xian-cong/Final-Year-Project-Nottingham/links and documents/project outline and planning report/Sample_Project Outline and Planning Report NJ-MEng-22-02-70_.pdf

## The University of Nottingham

## Faculty of Engineering

## Department of Electrical and Electronic Engineering

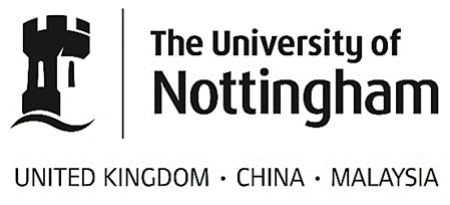
[picture p23: figure]

### EEEE4077 Project Outline and Planning Report

### Electrical Machine Condition Monitoring System

AUTHOR | : | Joel Wong Zi Xu
ID | : | 20208685
SUPERVISOR | : | Ir. Ts. Nandan Ganesh Jeyabalan
MODERATOR | : | Dr Mumtaj Begam
DATE | : | 21st Oct 2022

## Contents

1. Introduction | 1
2. Problem Statement | 1
3. Background Information | 2
3.1. Motor Faults | 2
3.2. Measurement of Vibration of Motors | 2
3.3. Measurement of Voltage of Motors | 3
3.4. Measurement of Current of Motors | 4
3.5. Measurement of Temperature of Motors | 4
3.6. Wave and Spectrum analysis | 5
3.7. IoT Technology | 6
4. Aim and Objectives | 6
4.1. Aim | 6
4.2. Objectives | 6
4.3. Deliverables | 6
5. Proposed Methodology | 7
6. Industrial Relevance | 7
7. Risk and Mitigations | 8
8. Project Timeline | 8
9. Appendix | i
References | i
Gantt Chart | iii
Project Specifications | iv

1

### 1. Introduction

As the operation of a motor continues in constant action, the likelihood of its failure increases as its operating conditions degrades and the machine becomes more and more vulnerable to wearing and aging. Based on the research, majority of motors become defective due to faults while only a mere 10% become inoperable due to old age [1]. Detecting faults before the occurrence of permanent damage is the intention of motor condition monitoring or alternatively, motor health monitoring, which is essential in preventing inner mechanical complications and prolonging the life of a motor [2].

Additionally with the advent of Internet of Things (IoT) technology, machines and devices are now able to be connected to exchange data with one another using the internet as its communication host [3]. Such technology has already been interfaced with the concept of motor condition monitoring in order to enhance the accessibility and control aspects of a motor health monitoring system. An example of such a system has proved its availability by allowing its user access to information of the motor, while away, by the usage of an Arduino compatible Wi-Fi module, the ESP8266, which in turn allows the motor monitoring system to pass the data from its motor monitoring sensors onto a webserver and therefore allowing access of its sensor information, via the internet, worldwide [4].

From literature review [1], [5], The condition of a motor is commonly measured through four parameters, these include: firstly, the motor temperature, which are usually used to gauge the condition of the bearing, ambient stator temperature. Secondly, the parameter of current which is used to determine the health of the windings as well as the mechanical system of the motor. Thirdly, the measurement of voltage which is used to judge the condition of the voltage supply as well as the power factor of the motor. Lastly, the intensity of the motor vibration which can be used to reveal issues in air-gap variation, misalignment, broken rotor bars and other mechanical motor faults.

This project focuses on the creation of a condition motoring system for a motor that is capable of detecting faults from the usage of information by sensors. Additionally, the system would also be interfaced with Wi-Fi technology in order to allow the information tracked to be available online and hence anywhere via the access of the internet.

### 2. Problem Statement

Failure of components awaits the operation of a motor the longer it remains in use as its parts are exposed to the wear and age from working [1]. The failure of parts of the motor vital to its functioning can begin to occur in the stator, rotor as well as upon the eccentricity of the motor where they are the result of the worn damaged parts which can include but are not limited to shorted coil windings, the breaking of rotor bars and the wearing of bearings respectively [6]. Consequently, the machine deteriorates as the faults add up, gradually becoming unreliable or even dangerous for operation. At the level of a large and complex industrial plant, the collection of failures is catastrophic and may result in the waste of millions of dollars for any rehabilitation and at the worst scenarios, a large-scale life-threatening accident [5]. The solution lies at the research of motor condition monitoring where the faults can be detected at the moment of their occurrence or even pre-occurrence and hence avoiding the disasters that may result from such motor failures.

2

### 3. Background Information

### 3.1. Motor Faults

As a motor remains in operation, wearing and aging can occur upon its body and this provides the root for the development of motor faults [1]. A machine fault can be described as any incident occurring within its machinery that obstructs the designed function of the machine [6]. Such faults can be defined into two categories: Internal faults, which includes component failures such as misalignment of motor sheets, coils, coupling, rotors & shaft, broken rotor bars or even damaged bearings whereas external faults are due to interactions with the loading, power supply as well as nearby environment and this includes overloading, environmental overheating, pollution and even unstable voltage [6]. The origin of faults are generally caused by stresses and careless operation, these can stem from several types, for instance, stator or armature faults are often traced to insulation problems which itself may be due to a collection of problems such as overheating of winding or stator core, loose bracing in the end winding, dirt contamination or even leaking from the cooling systems whereas damages of the rotor bar and end-rings mainly occur as a result of overheating, unbalanced magnetic forces, manufacturing issues as well as fatigued parts [7].

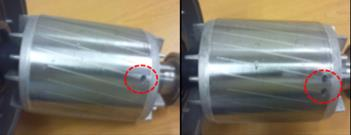
[picture p24: figure]

Figure 1: Rotor with one and two broken bars [8]

### 3.2. Measurement of Vibration of Motors

Vibrations generated by motors can be measured via the use of an accelerometer, through this, any vibrations produced as a result of any unintended impact of machinery can be detected; such vibration will appear at its characteristic frequency caused by the interference of the present defect [9]. As machinery failure usually manifests as vibration or as changes in vibration pattern due to their physical nature, vibration of motors is often used to monitor heavy physical defects that are often in rotation such as gears, shaft & rotors, rolling element bearings, journal bearings, flexible coupling as well as electrical machines [5]. The types of faults commonly to be detected via measurement of vibration are shown in Table 1:

3

Table 1: Faults that can be detected with vibration analysis [5]
Item | Fault
Gears | Tooth messing faults, Misalignment, Cracked and/or worm teeth, Eccentric gear
Rotors and shaft | Unbalance Bent shaft Misalignment Eccentric journals Loose components Rubs Critical speed Cracked shaft Blade loss Blade resonance
Rolling element bearings | Pitting of race and ball/roller Spalling Other rolling elements defect
Journal bearing | Oil whirl Oval or barrelled journal Journal/bearing rub
Flexible coupling | Misalignment Unbalance
Electrical machines | Unbalanced magnetic pulls Broken/damaged rotor bars Air gap geometry variations Structural and foundation faults Structural resonance Piping resonance Vortex shedding

### 3.3. Measurement of Voltage of Motors

The measurement of motor voltage is usually best suited to gauge the health of the supply voltage connected to the motor, via its phasing and balance, as well as the power factor of the motor [1]. Additionally, the measurement of the motor voltage has also been demonstrated to have the ability to replace the measurement of vibration in detecting physical faults as well as physical failure, for instance, a damaged rotor which exhibit high frequency disturbances to the

4

rotor mechanical speed will begin to affect the resultant magnetic field of the air gap as the rotor bar current fail to overcome the disturbance rapidly and hence causing induced voltages in the stator windings to be disturbed, therefore allowing possible detection of damaged rotor via voltage measurement [10].

### 3.4. Measurement of Current of Motors

To assess the condition of the motor windings as well as to gauge the load undertaken by the motor, the measurement of motor current can be performed [1]. Additionally, the current measured could be transformed into a decibel-frequency range via Fast Fourier Transform to provide information regarding frequencies due to fault which are affecting the general waveform of the current; fault can be detected as the current waveform measured would be different with and without the presence of faults [11], [12].

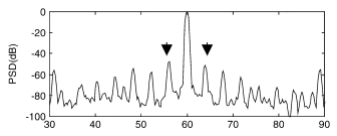
[picture p25: figure]

Figure 3: A Plotted Graph of MCSA of a Healthy Motor [8]

### 3.5. Measurement of Temperature of Motors

The motor temperatures can be determined via the usage of thermocouples, optical pyrometers, thermography, and resistance thermometer [5]. Temperatures measured in a motor are, in normal circumstances, generated from the magnetic losses within the rotor & stator, the resistive losses (I²R), friction as well as the motor windage [1]. Via temperature analysis, faults related to wearing due to insufficient lubricant can be monitored and prevented where additionally, the detection of overheating, which can subject organic material within the insulation of the stator winding to deteriorate, can also be identified, and mitigated [5].

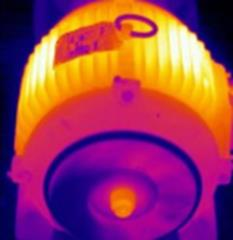
[picture p26: figure]

Figure 4: Thermal RGB image of a motor showing levels of temperature throughout motor [13]

5

### 3.6. Wave and Spectrum analysis

The most common two ways to analyse and detect faults and failures within a motor is, firstly, by performing a time-domain analysis which is via inspecting the measured data (ie. Voltage, Temperature, Current, Vibration, etc.) from the sensors as a plot against the time as this allows a clear investigation of the direct and raw data from the sensor output; the second method is by converting the time-domain measured data into the frequency domain, typically done using fast Fourier transform (FFT), where faults can be observed due to their specific unique frequencies generated to due to their existence appearing as peaks alongside the expected frequencies of a normal working motor should the motor in evaluation possesses one or more faults [5]. An example of this has been mentioned with the description of MCSA where the current measured could be represented as a decibel-frequency via Fast Fourier Transform [10]. Similarly, another example can be found in the frequency spectrum of the vibrations measured, done using Fourier Transform, where the frequency of each component is known and hence where the peaks appear at the frequency of that particular component, a fault can be confirmed to exist at that particular component [9]. Furthermore, as the existence of noise may be recorded as well such that the frequency spectrum represented might be disturbed and become inaccurate, averaging of the values before the conversion into the frequency spectrum could be done to reduce the presence of noise [11]. From this, it can also be concluded that the use of multiple types of spectrum analysis (ie. Voltage, current, vibration, etc.) can be done for each fault in order to clearly assess the existence of faults and avoid errors.

Figure 5: Voltage Frequency Spectrum of a motor with Broken Rotor Bars at 80% of the motor full load [8]

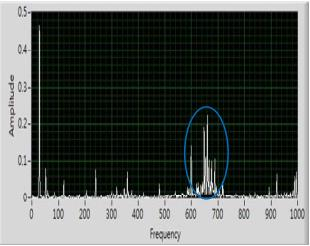
[picture p27: figure]

Figure 6: Vibration Frequency Spectrum of a motor indicating fault at the rotor [14]

6

### 3.7. IoT Technology

Internet of Things (IoT) can be defined as the connection of devices and objects to share data and to communicate using the internet as a pathway [3]. Through the usage of this technology, complications due to physical components necessary for data transfer between sensors in condition motoring are eliminated, additionally, the absence of wires allows better strategical placement of the sensors onto positions previously inconceivable due the space needed for the physical trail of wires connected [15]. An example of such a system which integrates IoT and Motor Condition Monitoring has been demonstrated to be possible where the system was capable of measurement of Voltage, current as well as vibration along with the fact that it can detect the existence of faults and alert the user anytime at its occurrence, wirelessly to anywhere through an internet connection [4].

### 4. Aim and Objectives

### 4.1. Aim

The main focus of this project is to design and program a condition monitoring system for electrical machines with the ability to transfer its recorded information over a wireless transfer data system with a user interface

### 4.2. Objectives

- Design and develop a condition monitoring system for the electrical machines.
- Analyse the performance by monitoring the condition of electrical machines using the developed system.
- Classify the abnormalities found in monitoring the electrical machines by suing the developed system.
- Develop a wireless transfer data system to integrate with the developed system for user interface.

### 4.3. Deliverables

- Identify the parameters of the electrical machines that will be used for condition monitoring.
- Design the condition monitoring system by integrating with the electrical and mechanical sensors.
- Test the developed system to ensure the condition of the machines is monitored based on the relevant parameters.
- Develop a wireless transfer data system to transfer the monitored parameters for user interface.

7

### 5. Proposed Methodology

- Literature review and Research: At the initial stages of the project, the essentials of motor condition monitoring would need to be understood. The various types of faults occurring within a typical motor as well as the methods utilized for faults detection would need to be familiarized for the identification of failures. Additionally, concepts related to IoT technology and software would need to be read upon for the basis of a wireless transfer data system. Lastly, a study upon tutorials would need to be carried out in order for the proper usage of the different sensors and modules
- Integration of Sensors to the Motor: The identification of errors stems pivotally from the positioning of the sensors to the right connection relative to the motor in evaluation in order for accurate detection of faults
- Programming Wireless Transfer of Data from Sensors: Coding of a program as well as strategic integration of a Wi-Fi module to acquire and manage information gathered by the sensor to display over to the user of the system, wirelessly
- Simulating Faults: Motors have to be physically manipulated in order to mimic the condition of a faulty motor so as to assess the validity of the constructed condition monitoring system via comparison of detected data and faulty pattern of information from reviewed literature
- Classifying Faults: Information from different sensors have to be integrated cohesively both physically and through the developed program in order to determine the pattern of data that will occur when measured by different sensors for each specific fault

### 6. Industrial Relevance

On the scale of large industrial manufacturing plants, failure of machines such as a motor within its complex process would risk expensive operating costs due to maintenance of incapacitated components, the loss of possible production that could have been without the occurrence of failed machines as well as putting the lives of operation crew members in serious endangerment [5].

To prevent such complications, logically, the failure or faults of the machine must be detected at its occurrence or even prior to it. In condition monitoring of motors, failures such as stator winding and rotor faults can be reliably detected as each type of fault appear with distinct characteristics such as when measured with a vibration sensor (accelerometer), current sensor or even a voltage sensor which means that faults have the possibility of being instantly identified and hence preventing resulting consequences [8], [9]. To further ensure proper monitoring of a large complex plant, several types of strategic maintenance of the components could be carried out of which motor condition monitoring could be advantageous to. Firstly, there exists a predictive type of maintenance known as Condition-based maintenance which is maintenance done where restoration of a part is initiated due to noticeable wearing detected as result of a change in its monitored parameter [5]. Other types of maintenance include proactive maintenance which is based on analysis of failure as well as preventative maintenance which include checkups once every duration in a set time; the implementation of such strategies has been analyzed to eliminate factory downtime as well as in assisting the avoiding of mistakes which directly leads to enhancing the efficiency of a plant to its fullest potential [16].

8

Additionally, the rise of IoT and its integration means condition monitoring does not have to be physical presence based as the information from sensors can be passed via the internet and hence allowing workers to monitor motors even while away from the workplace [4].

### 7. Risk and Mitigations

In this project, several types of sensors and modules are implemented to create a sensor system, each with its own unique set of programming code for the manipulation of its sensor, as such, the combination of all sensors and its individual programming to exchange data may prove to be time-consuming and difficult. To ease the process, certain sensors should be programmed and worked on first before integrating other sensors to prevent a chaotic combination of programming. Furthermore, there could exist a limit to the type of fault that can be allowed to be simulated for testing purposes due to the dangerous nature of certain failure such as, but are not limited to, high current short circuit of the stator winding as well as high speed rotation of broken rotor bars. To avoid serious injury, the use of personal protective equipment (PPE) such as safety googles could be utilized as well as performing the simulated of faults during the presence of the supervisor to prevent accidents due to inexperience.

### 8. Project Timeline

In the Autumn semester, the focus of tasks will be on Literature review upon the various types of faults, the ways to detect them as well as forming the basis of wireless transfer of data from sensors. Later, the integration of sensors to the motor would be carried out before the simulation of faults can be done to confirm the validity of the measurement of the sensors as well as to record motor fault behaviour. In the Spring Semester, the development of a wireless data transfer program with the ability to classify motor faults can be worked upon based on the work from the previous semester before the final task of motor fault classification from the data of various sensors will be carried out. More details of the time plan can be found in the Gantt Chart in the appendix.

i

### 9. Appendix

References

[1] R. Loiselle, Z. Xu, and I. Voloh, “Essential motor health monitoring,” Record of Conference Papers - Annual Petroleum and Chemical Industry Conference, vol. 2016-March, no. December, pp. 8–13, 2016, doi: 10.1109/PCICON.2015.7435126.
[2] D. Mirabbasi, G. Seifossadat, and M. Heidari, “Effect of unbalanced voltage on operation of induction motors and its detection,” ELECO 2009 - 6th International Conference on Electrical and Electronics Engineering, pp. 189–192, 2009.
[3] T. Muhonen, H. Ailisto, and P. Kess, “Standardization in Industrial internet (IoT) and Condition-Based Maintenance,” Proceedings at the Automaatio XXI …, no. March, 2015, [Online]. Available:
https://www.researchgate.net/profile/Heikki_Ailisto/publication/277668082_Standardization_in_Industrial_internet_IoT_and_Condition-Based_Maintenance/links/5570007508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
[4] N. Khan, F. Rafiq, F. Abedin, and F. U. Khan, “IoT Based Health Monitoring System for Electrical Motors,” pp. 6–11, 2019.
[5] P. Jayaswal, A. K. Wadhwani, and K. B. Mulchandani, “Machine fault signature analysis,” International Journal of Rotating Machinery, vol. 2008, 2008, doi: 10.1155/2008/583982.
[6] A. J. Bazurto, E. C. Quispe, and R. C. Mendoza, “Causes and failures classification of industrial electric motor,” Proceedings of the 2016 IEEE ANDESCON, ANDESCON 2016, pp. 4–7, 2017, doi: 10.1109/ANDESCON.2016.7836190.
[7] A. Choudhary, D. Goyal, S. L. Shimi, and A. Akula, “Condition Monitoring and Fault Diagnosis of Induction Motors: A Review,” Archives of Computational Methods in Engineering, vol. 26, no. 4, pp. 1221–1238, 2019, doi: 10.1007/s11831-018-9286-z.
[8] A. Shaeboub, M. Lane, U. Haba, F. Gu, and A. D. Ball, “Detection and diagnosis of compound faults in induction motors using electric signals from variable speed drives,” 2016 22nd International Conference on Automation and Computing, ICAC 2016: Tackling the New Challenges in Automation and Computing, no. September, pp. 306–312, 2016, doi: 10.1109/IConAC.2016.7604937.
[9] R. K. Patel, S. Agrawal, and N. C. Joshi, “Induction motor bearing fault identification using vibration measurement,” 2012 Students Conference on Engineering and Systems, SCES 2012, no. June 2015, 2012, doi: 10.1109/SCES.2012.6199058.
[10] F. Dalvand, A. Kalantar, S. Shokoohi, and H. Bevrani, “Time-domain bearing condition monitoring in induction motors using instantaneous frequency of motor voltage,” pp. 1–7, 2015, doi: 10.1109/sgc.2014.7150708.
[11] E. Geetha and C. Nagarajan, “Induction Motor Fault Detection and Classification Using Current Signature Analysis Technique,” Proc. IEEE Conference on Emerging Devices and Smart Systems, ICEDSS 2018, no. March, pp. 48–52, 2018, doi: 10.1109/ICEDSS.2018.8544272.
[12] M. Irfan, N. Saad, R. Ibrahim, and V. S. Asirvadam, “An intelligent diagnostic system for the condition monitoring of AC motors,” Proceedings of the 2013 IEEE 8th Conference on Industrial Electronics and Applications, ICIEA 2013, pp. 1248–1253, 2013, doi: 10.1109/ICIEA.2013.6566558.

ii

[13] S. Badoni and R. K. Jarial, “Health Monitoring of three phase induction motor using infrared thermography,” Proceedings of the 6th International Conference on Communication and Electronics Systems, ICCES 2021, pp. 156–160, 2021, doi: 10.1109/ICCES51350.2021.9489095.
[14] J. L. Jiang, H. C. Chang, and C. C. Kuo, “Operating monitoring and fault types classification for motors through vibration signal,” Proceedings - 2016 IEEE International Symposium on Computer, Consumer and Control, IS3C 2016, pp. 61–64, 2016, doi: 10.1109/IS3C.2016.26.
[15] X. Xue, V. Sundararajan, and W. P. Brithinee, “THE APPLICATION OF WIRELESS SENSOR NETWORKS FOR CONDITION MONITORING,” pp. 12–15.
[16] M. M. O. Kane and M. J. Sander, “Intelligent Motors Moving To The Forefront Of Predictive Maintenance”.

iii

Gantt Chart

Year 4 Individual Project Gantt Chart

Supervisor: Ir. Ts. NANDAN GANESH JEYABALAN | Legends: | Week of Moderator Meeting:
Project Code: NJ-MEng-21-02 | | Milestone:
Autumn Semester | Study Week | Exam | CNY Break | H Raya Spring Semester Break
| | October | | | January | February | March
| | | | | | November | | WEEK 13 | December WEEK 9 | WEEK 26 | WEEK 30 Tasks | April WEEK 22

Planning For Project Location and item Requirements HIRARC form and Securing Lab Workspace
Hardware Inspection and Sensor Component Research Finalising Project Objectives and Project Specification Hardware Research and Purchase Cost Estimation Writing Project Outline and Planning Report

Submition of Project Outline and Planning Report

SeptWEEK 4 | WEEK 5 | WEEK 6 | WEEK 7 | WEEK 8 | WEEK 10 | WEEK 11 | WEEK 12 | WEEK 14 | WEEK 15 | WEEK 16 | WEEK 17 | WEEK 18 | WEEK 19 | WEEK 20 | WEEK 21 | WEEK 23 | WEEK 24 | WEEK 25 | WEEK 27 | WEEK 28 | WEEK 29 | WEEK 31 | WEEK 32 | WEEK 33 | WEEK 34 | WEEK 35

Researching and Studying Electrical Machine Condition Monitoring Methods

Researching of Common Electrical Motor Faults
Literature Review of Electrical Machine Condition Monitoring via Sound and Vibration Literature Review of Electrical Machine Condition Monitoring via Voltage and Current Literature Review of Electrical Machine Condition Monitoring via Temperature Literature Review of Electrical Machine Condition Monitoring using IoT technology

Designing and Setting up Induction Motor Condition Monitoring System

Researching and Learning the Function of the Sensors and WIFi Module Coding of Program to Manage the Monitoring of Sensors and WiFi Module Physically Intergrating Sensors onto the Motor
Running Induction Motor to Ensure Accurate Measurement by Sensors Simulating Induction Motor Faults to Record Specific Motor Fault Behaviour

Development of Wireless Transfer Data System Interface

Coding of Program to Display User Interface for the Condition Monitoring System Coding of Program to Connect Software User Interface to Sensors used in Monitoring Coding of Program to Display the Correct Fault Information in Relation to the Detection

Classification of Motor Faults in the Motor Condition Monitoring System
Linking Pattern of Information detected from Different Sensors into the Common Fault Detected
Coding of Program to Display the Correct Fault Information from multiple Sensors in Relation to the Detection

Thesis, Documents and Presentation Writing Sections of Draft Thesis

Draft Thesis submission Writing Sections of Final Thesis

Final Thesis & Logbook Submission Preparation of Roadshow
Presentation and Viva Preparation

Student Name: Joel Wong Zi Xu Student ID: 20208685

iv

Project Specifications
Project Code | NJ-MEng-22-02
Supervisor | Ir. Ts. Nandan Ganesh Jeyabalan
Moderator | Dr Mumtaj Begam

Project
Description

Project Title: Electrical Machine Condition Monitoring System

The term reliability is a criterion that must be considered when selecting an electrical machine and its drive system for a particular load. As the cost of machines and drives varies proportionally to their reliability status, studies have been conducted throughout the world to achieve one ultimate goal – to produce a machine and drive system with higher reliability and minimum cost spent in manufacturing it. Therefore, condition monitoring is an important part in ensuring the performance and life span of the electrical machines maintained and improved. This project aims to design an Electrical Machine Condition Monitoring System in order to better monitor the performance and improve the overall efficiency of the electrical machines.

Project Objectives | 1. Design and develop a condition monitoring system for the electrical machines. 2. Analyse the performance by monitoring the condition of electrical machines using the developed system. 3. Classify the abnormalities found in monitoring the electrical machines by suing the developed system. 4. Develop a wireless transfer data system to integrate with the developed system for user interface.
Project Deliverables | 1. Identify the parameters of the electrical machines that will be used for condition monitoring. 2. Design the condition monitoring system by integrating with the electrical and mechanical sensors. 3. Test the developed system to ensure the condition of the machines is monitored based on the relevant relevant parameters. 4. Develop a wireless transfer data system to transfer the monitored parameters for user interface.
Target Discipline (You may check both) | ☑ Electrical and Electronic ☐ Mechatronic

v

HW/SW/Research Ratio | HW | SW | Research/Investigation/Design/Math
| 50 | 30 | 20
Lab Space Requirements | ☒ Fixed Space ☐ Ad-hoc Space ☐ Others. Please state.
Software (This is software usually supportedin the Software Lab) | Python, Arduino Programming Codes
Prepared By: | Reviewed By:
Ir. Ts. Nandan Ganesh Jeyabalan | Dr Mumtaj Begam
30th of September 2022 | 12 Oct. 2022
(Supervisor) | (Moderator)

# Electrical Machine Condition Monitoring System

# by Joel Zi Xu Wong

### Submission date: 24-Oct-2022 04:47PM (UTC+0100)

## Submission ID: 187347788 File name:

243058_Joel_Zi_Xu_Wong_Electrical_Machine_Condition_Monitoring_System_6299887_1057029960.pdf (525.9K)

## Word count: 4284 Character count: 25819

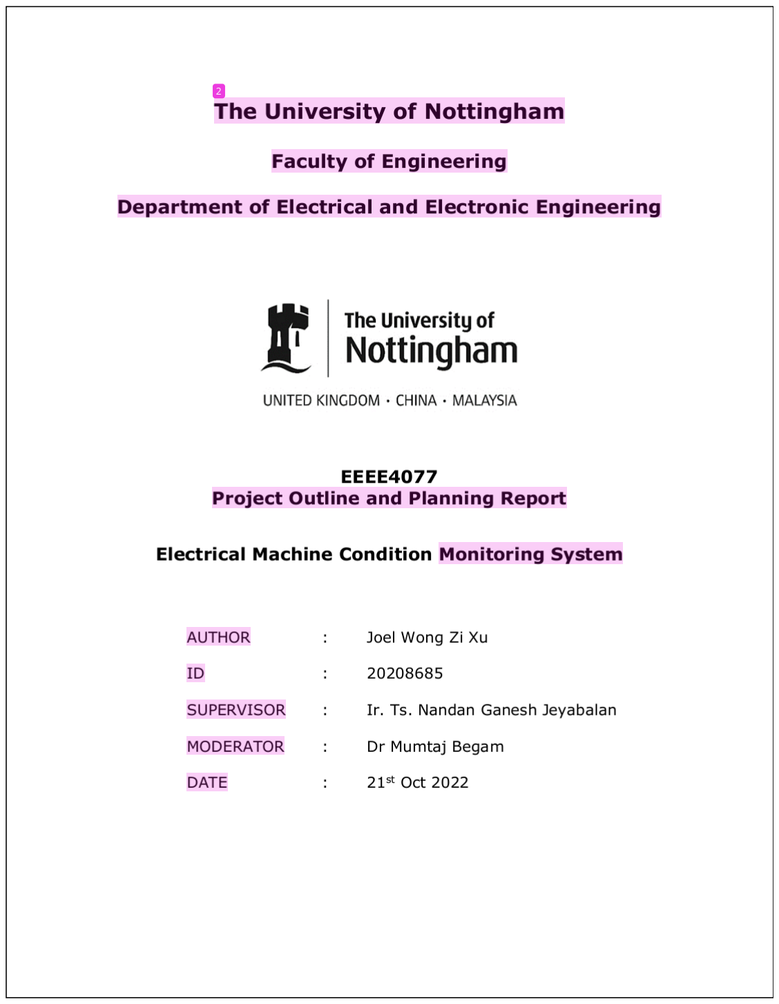
[picture p28: page 17]

2

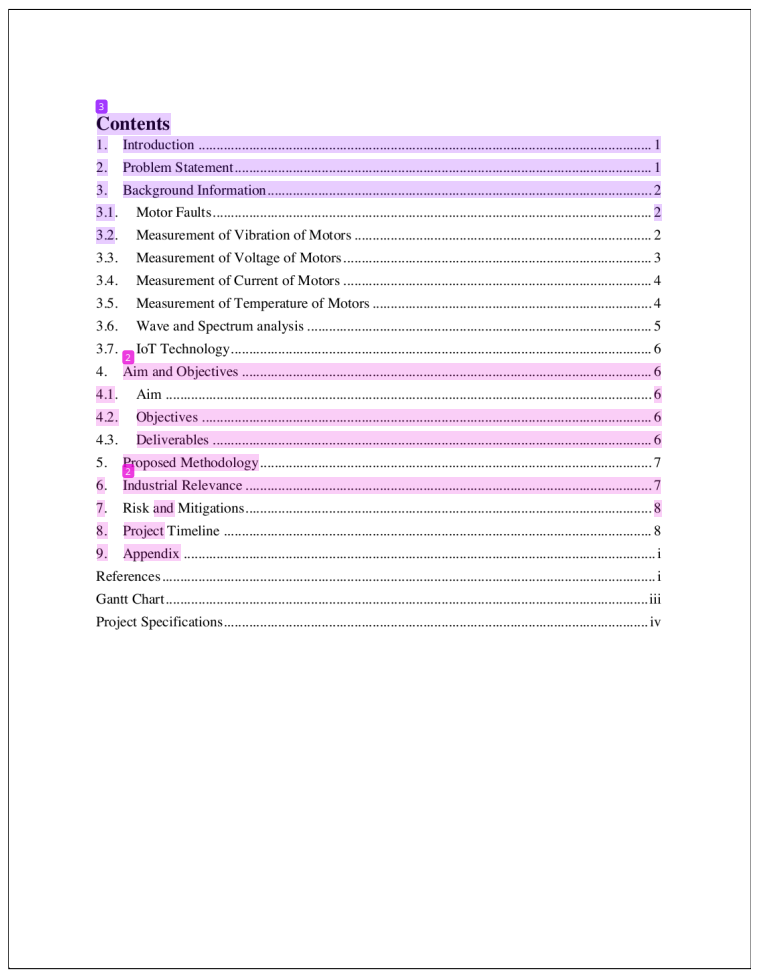
[picture p29: page 18]

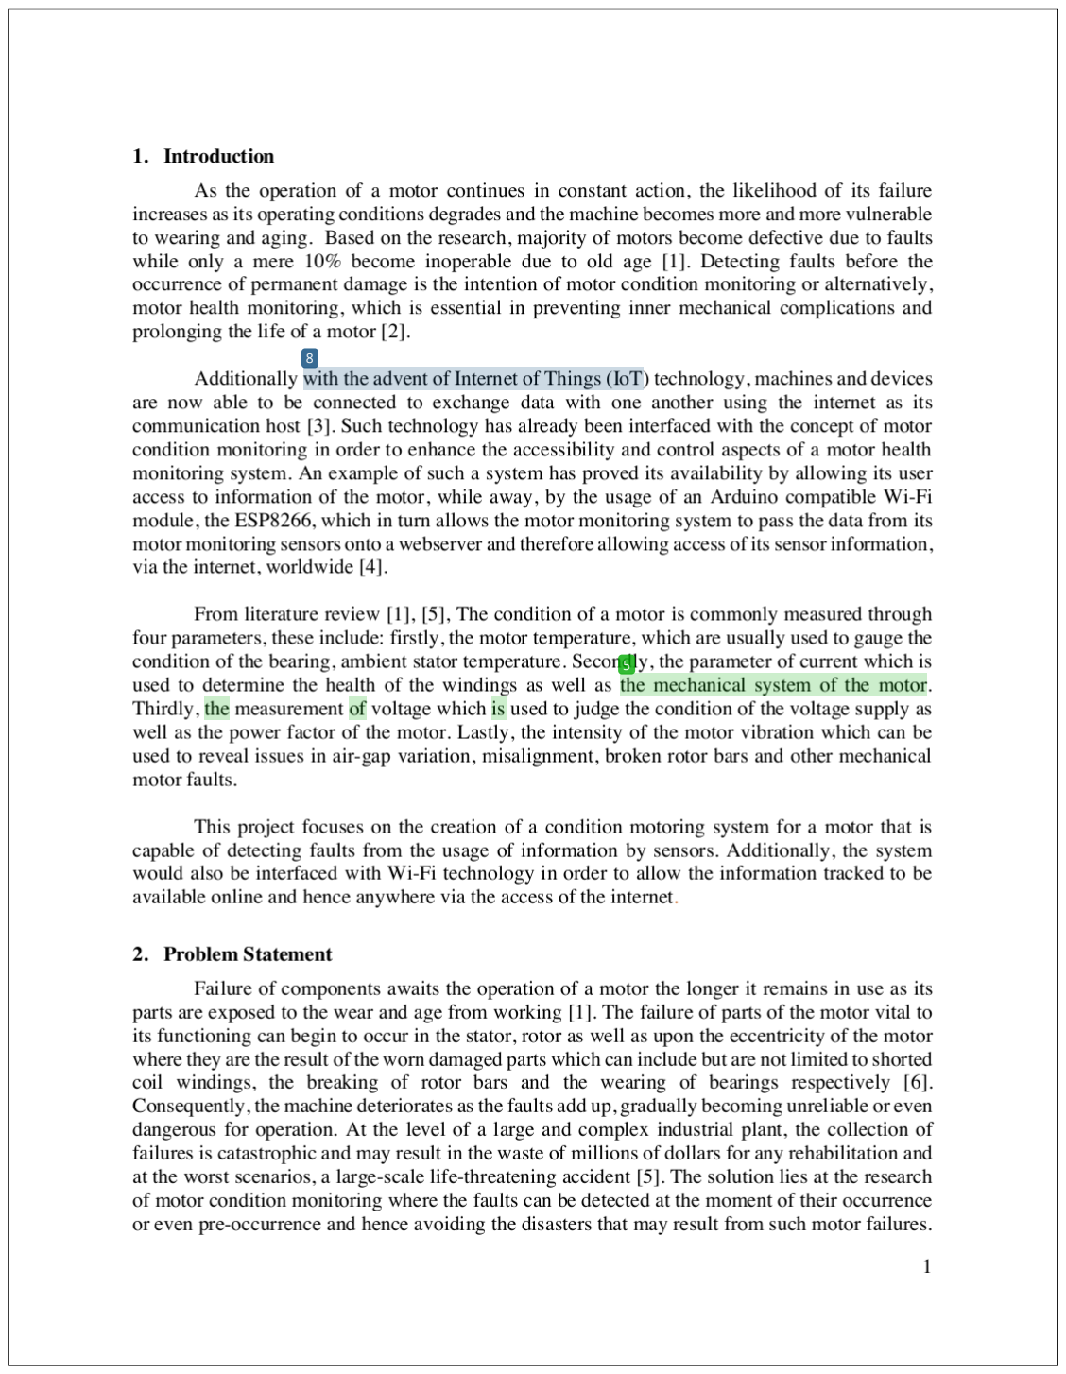
[picture p30: page 19]

5

8

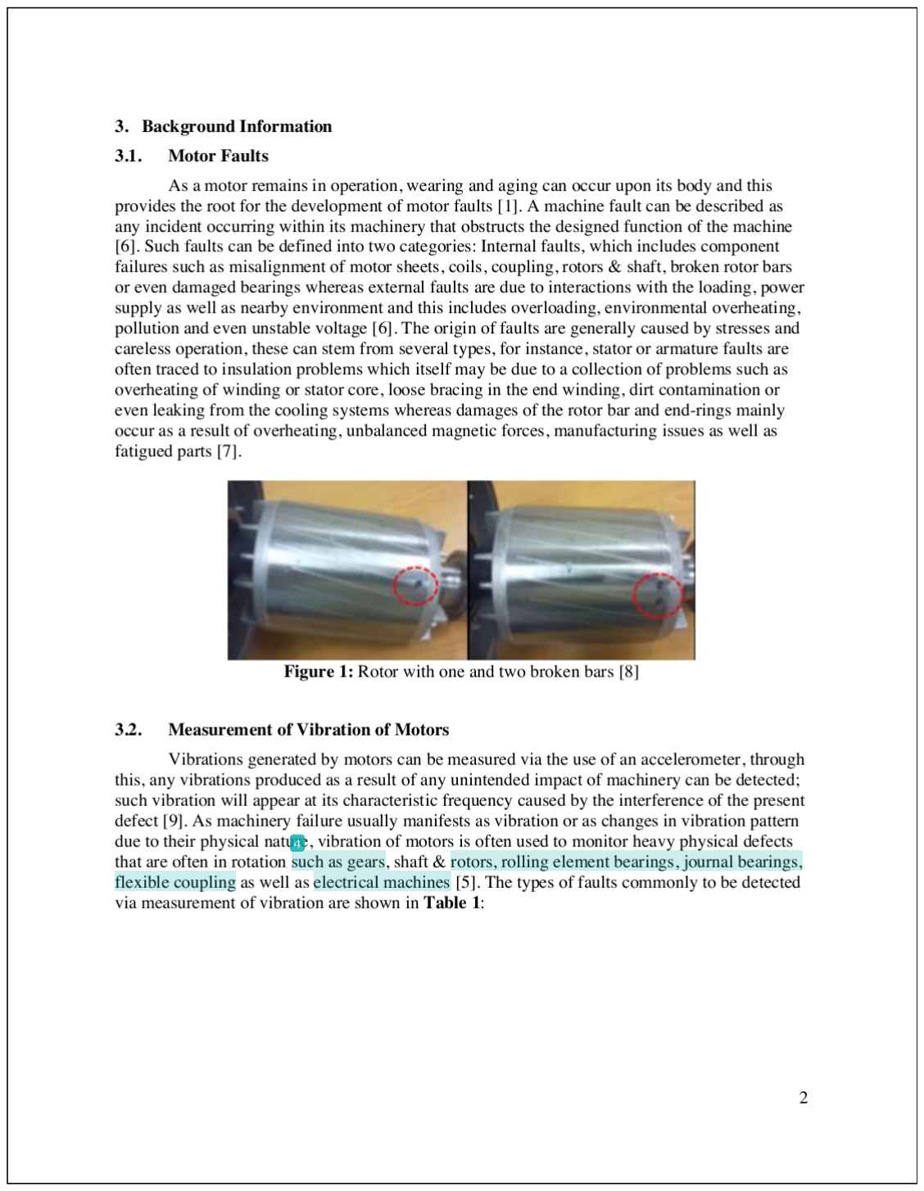
[picture p31: page 20]

4

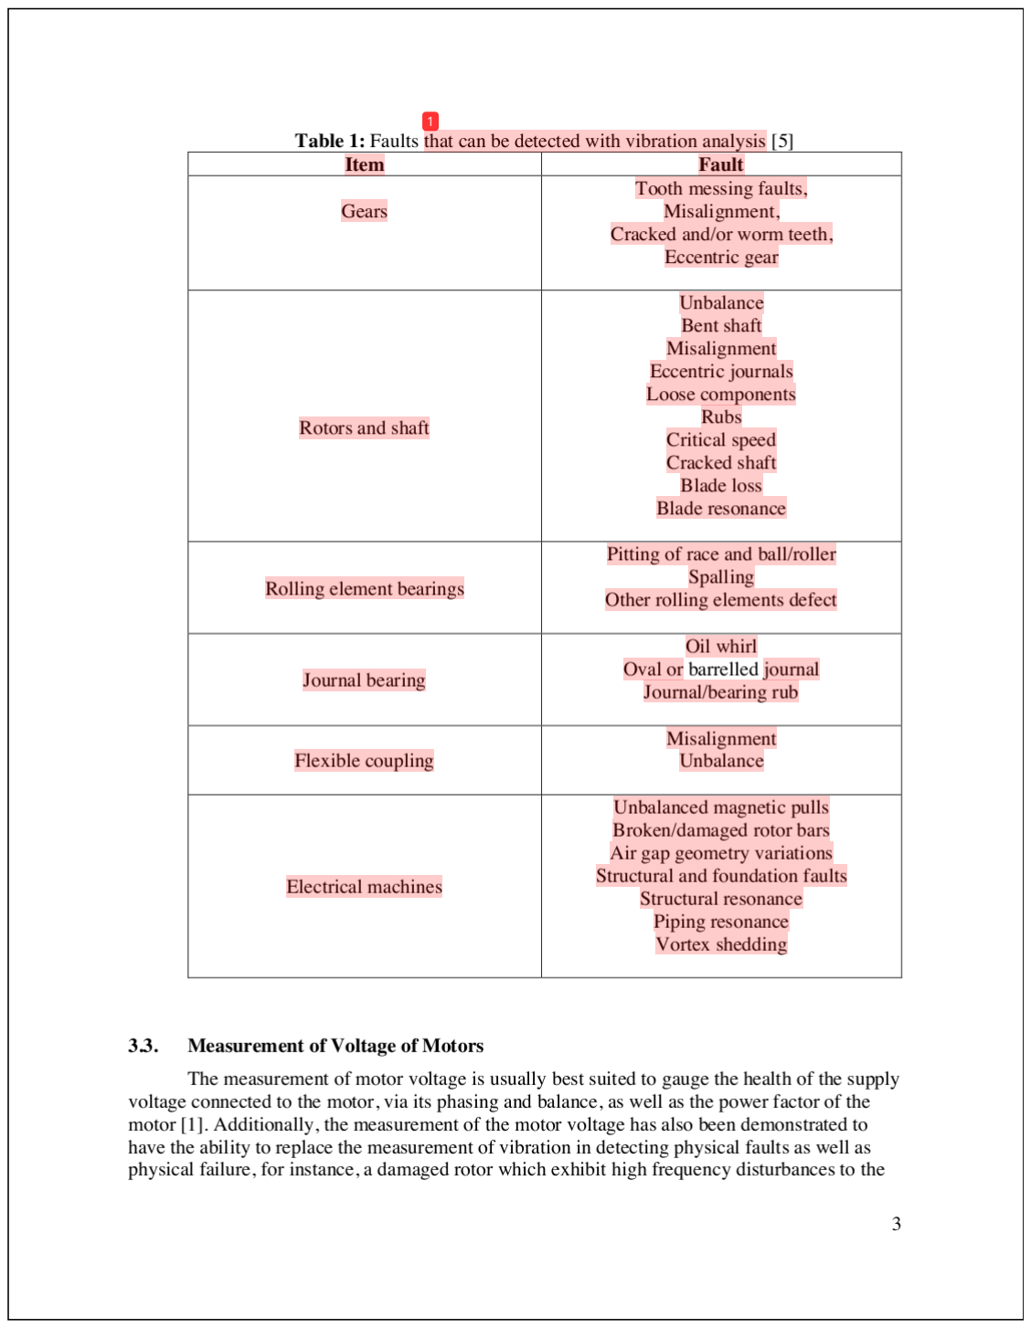
[picture p32: page 21]

1

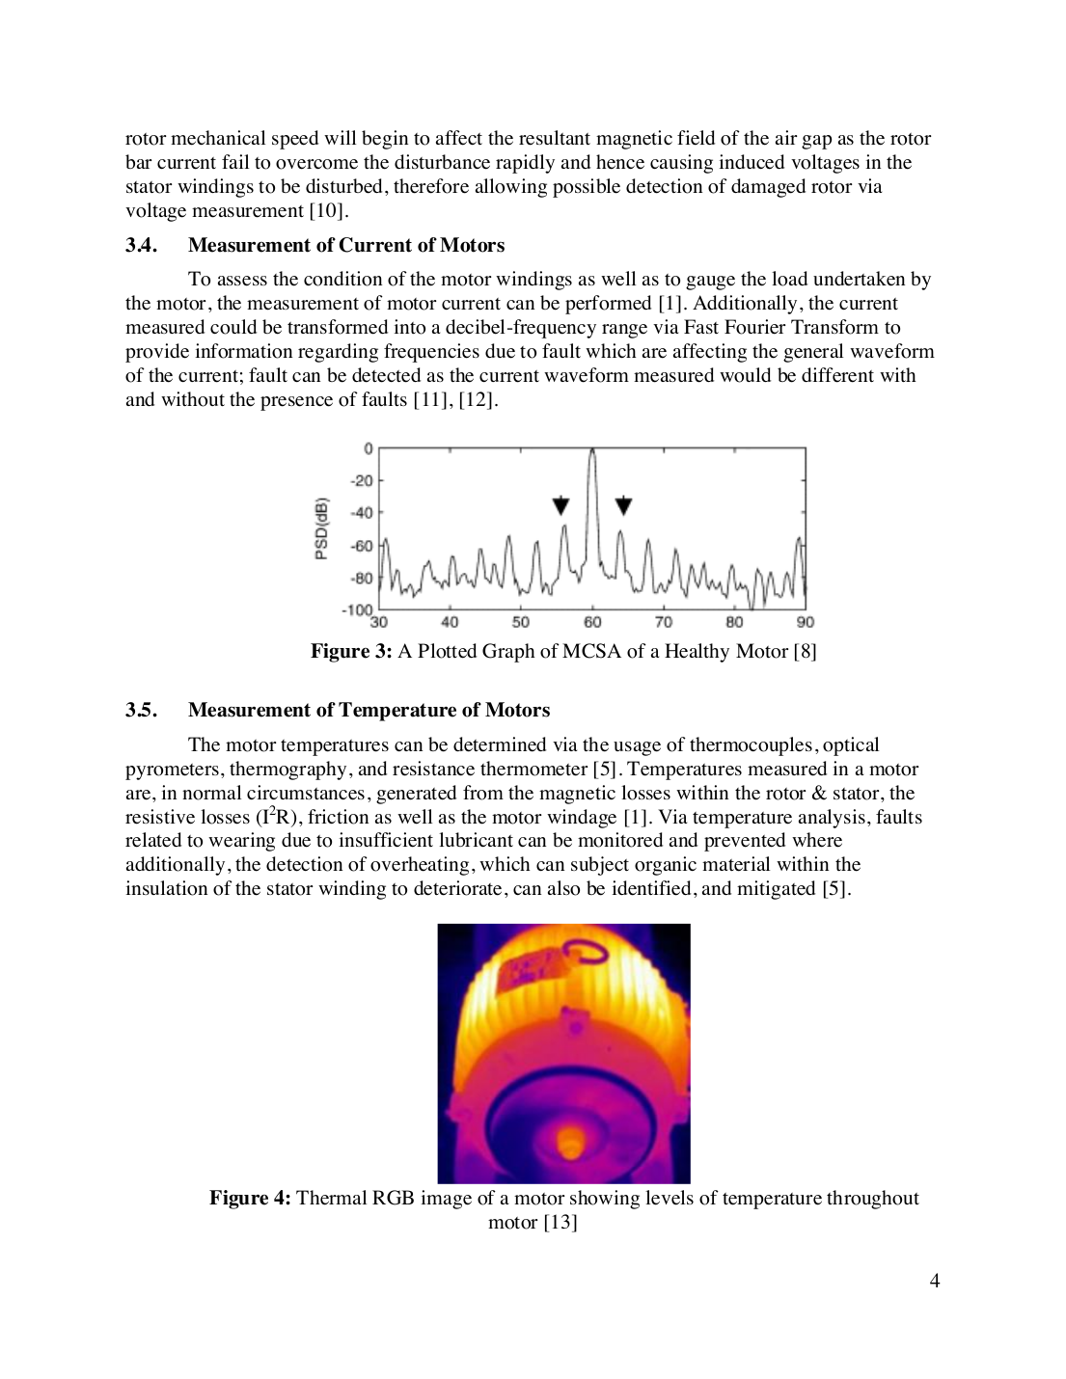
[picture p33: page 22]
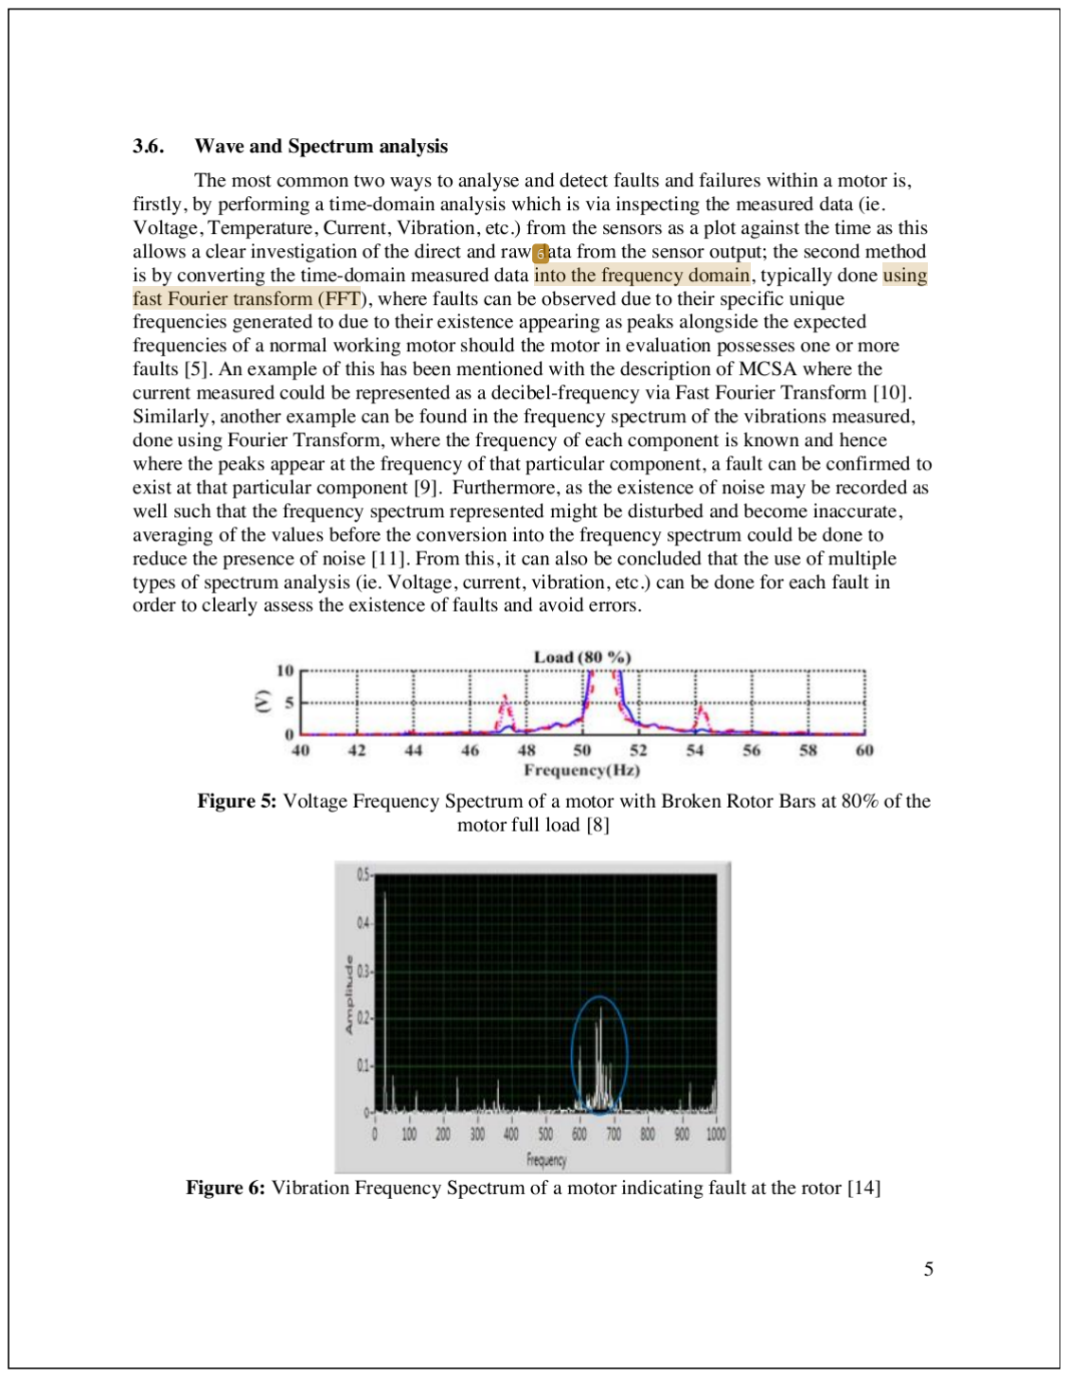
[picture p34: page 23]

6

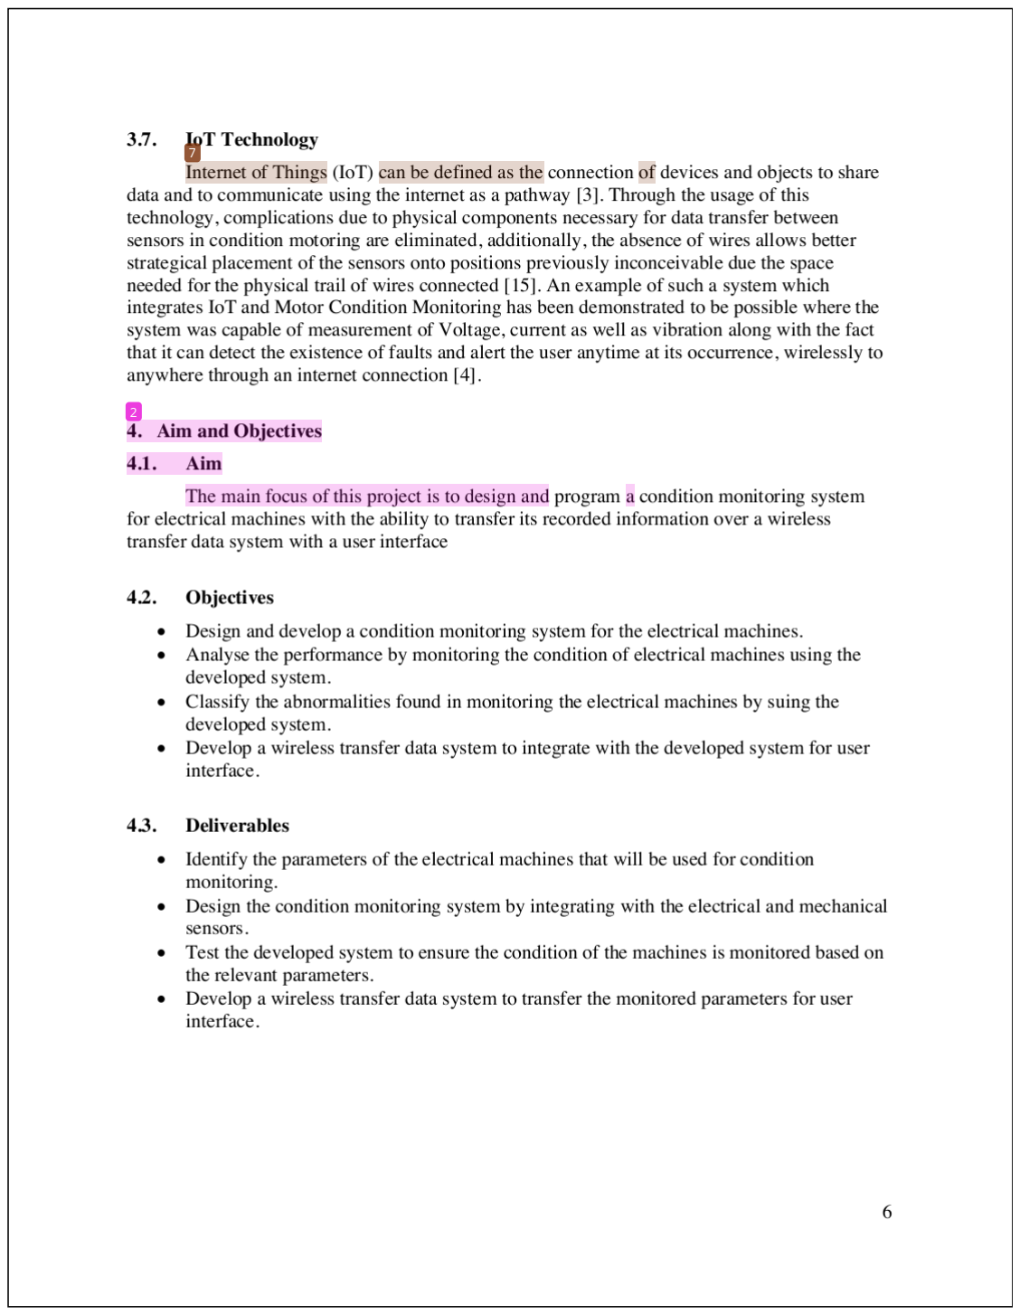
[picture p35: page 24]

2

7

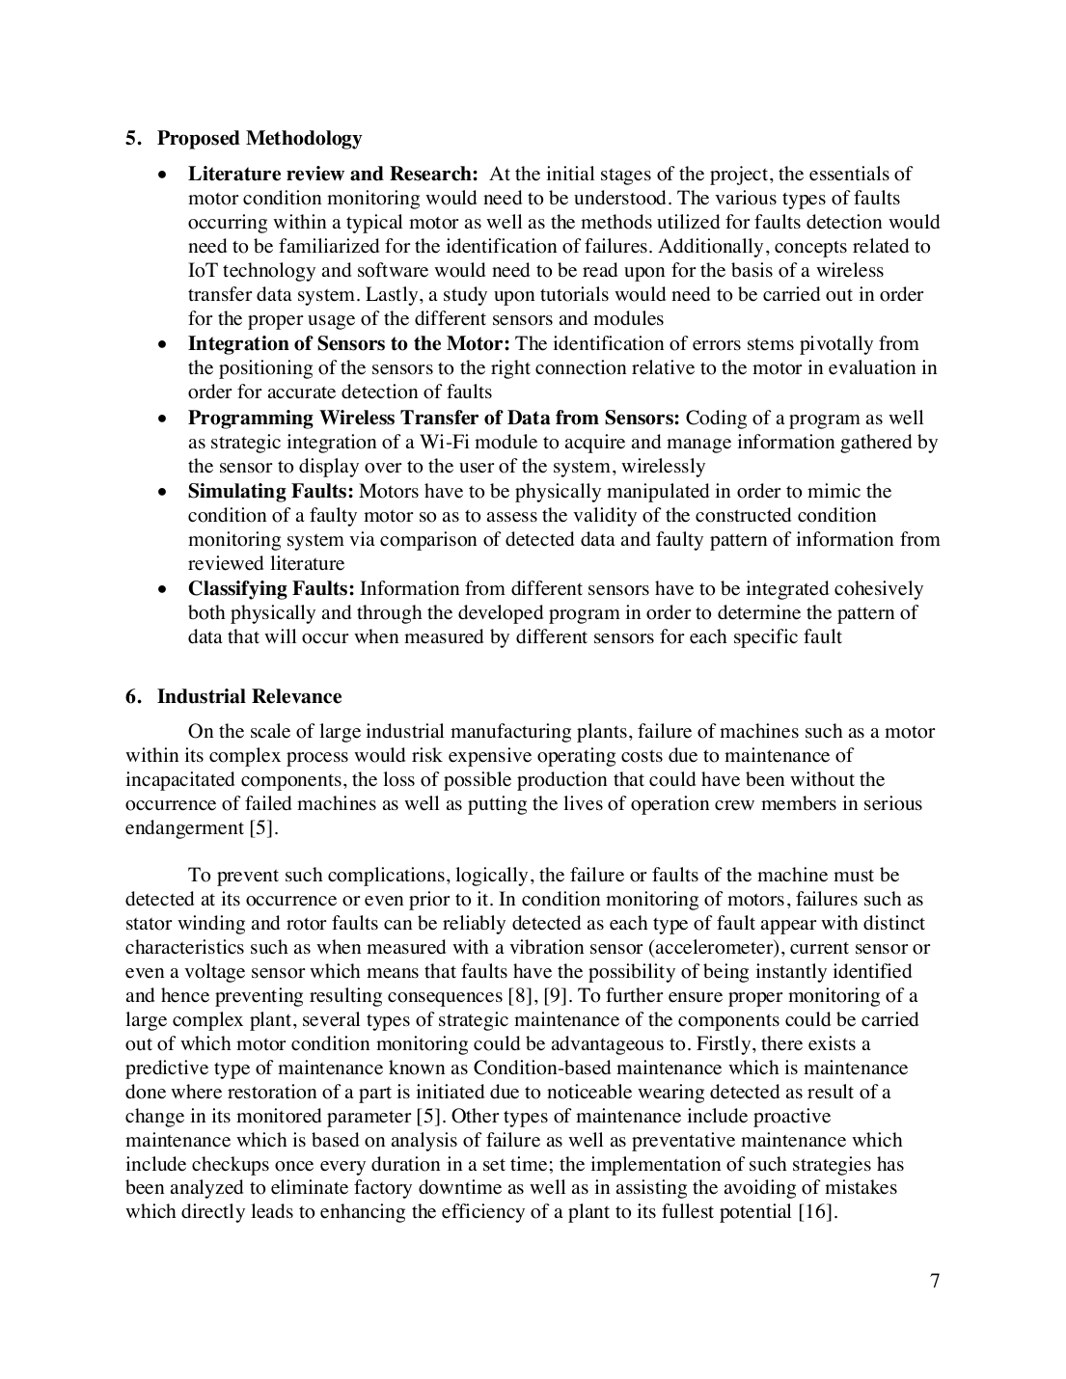
[picture p36: page 25]
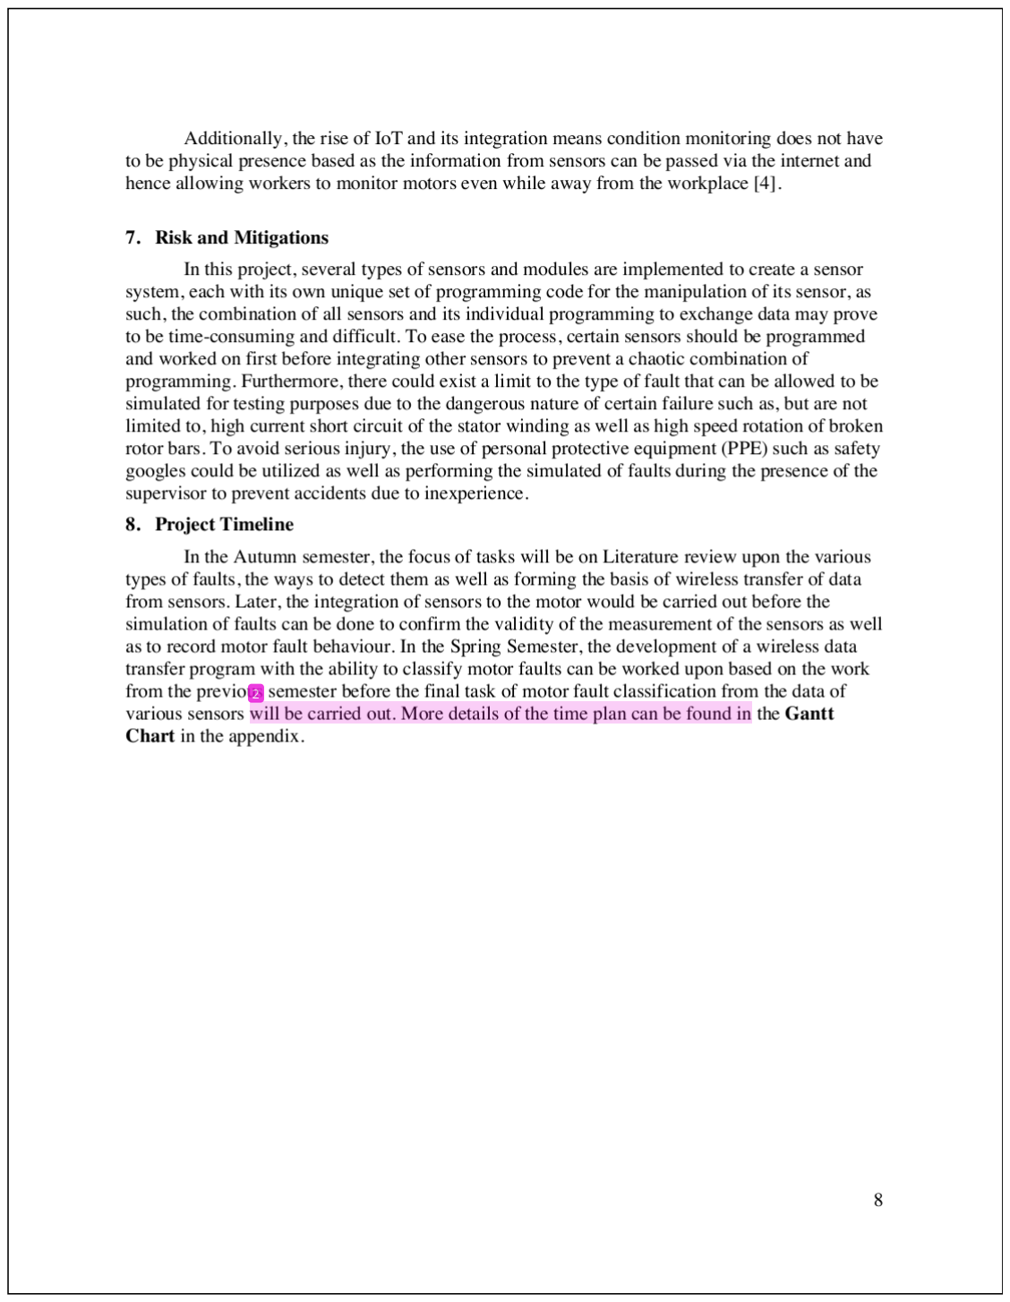
[picture p37: page 26]

2

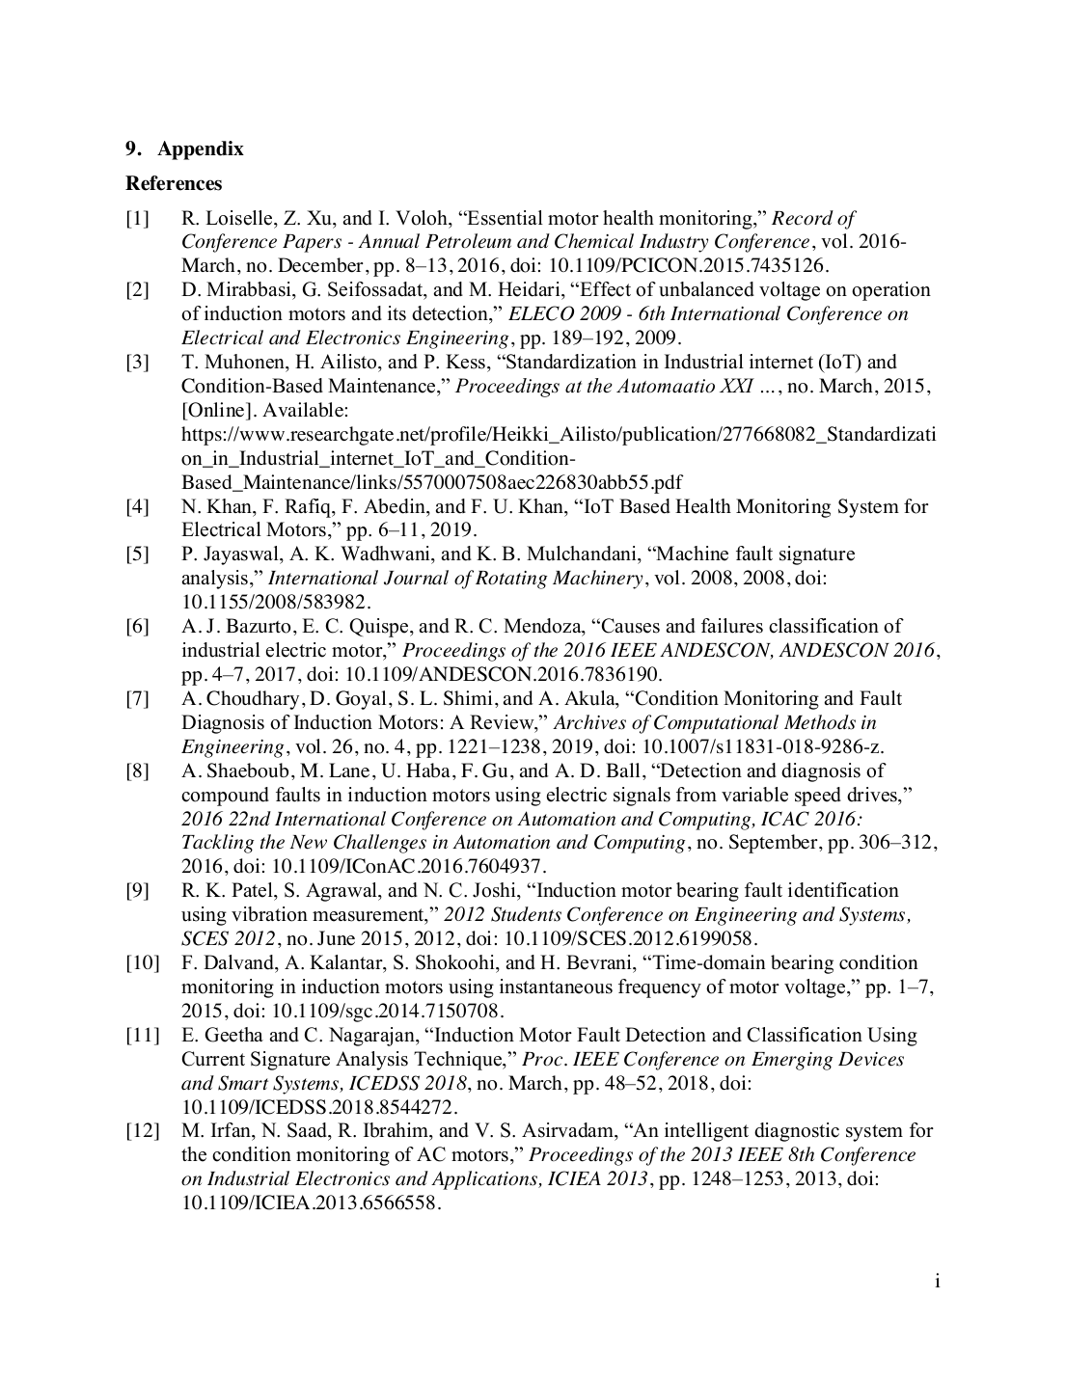
[picture p38: page 27]
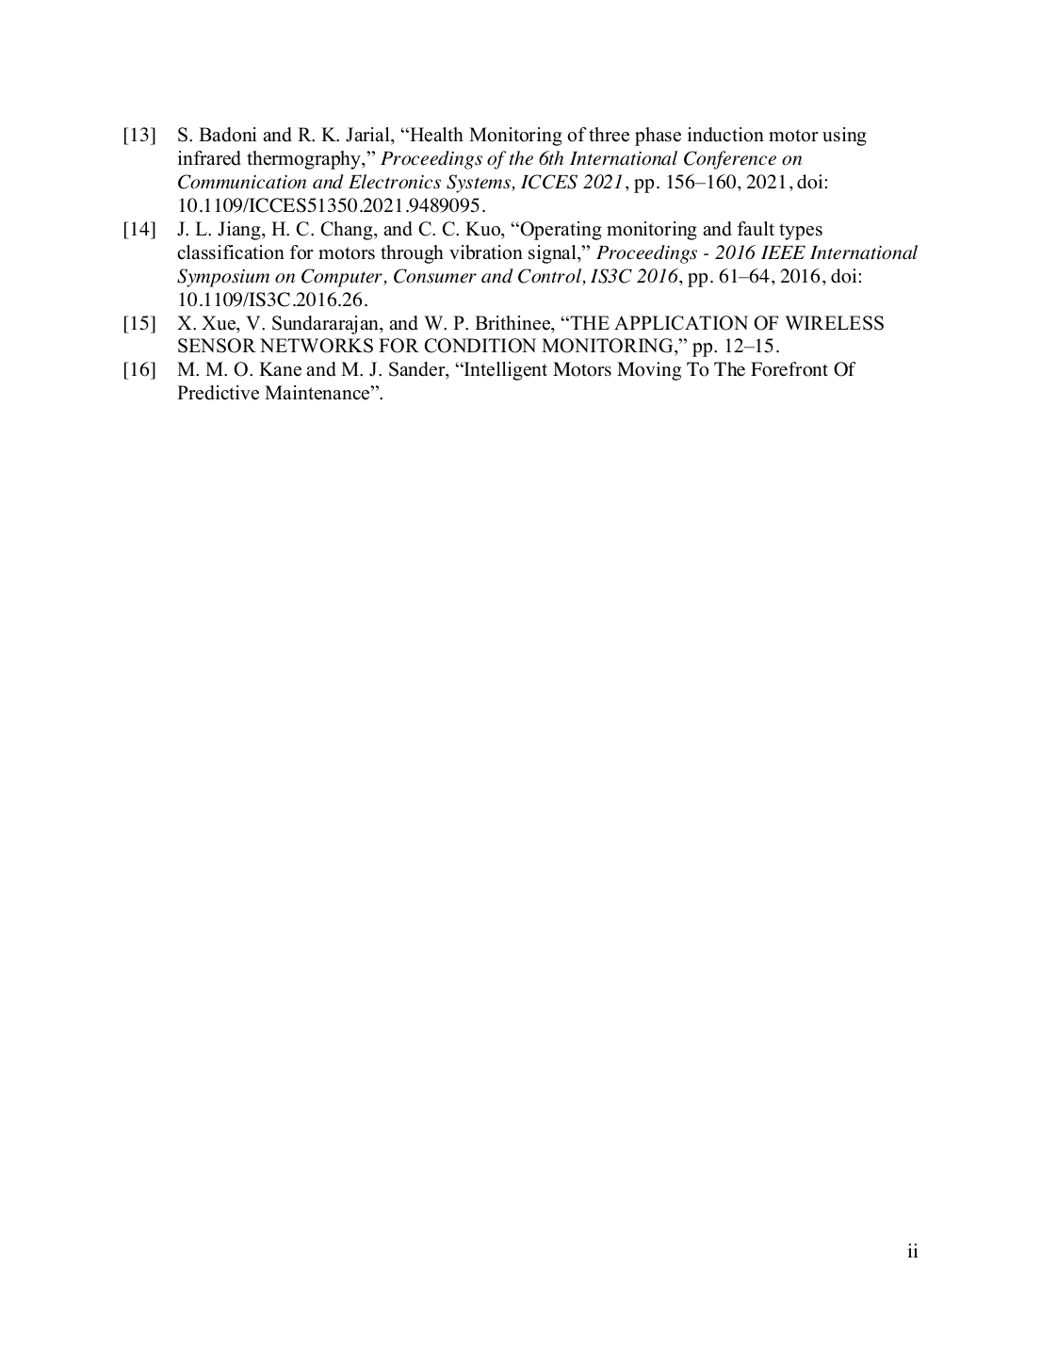
[picture p39: page 28]
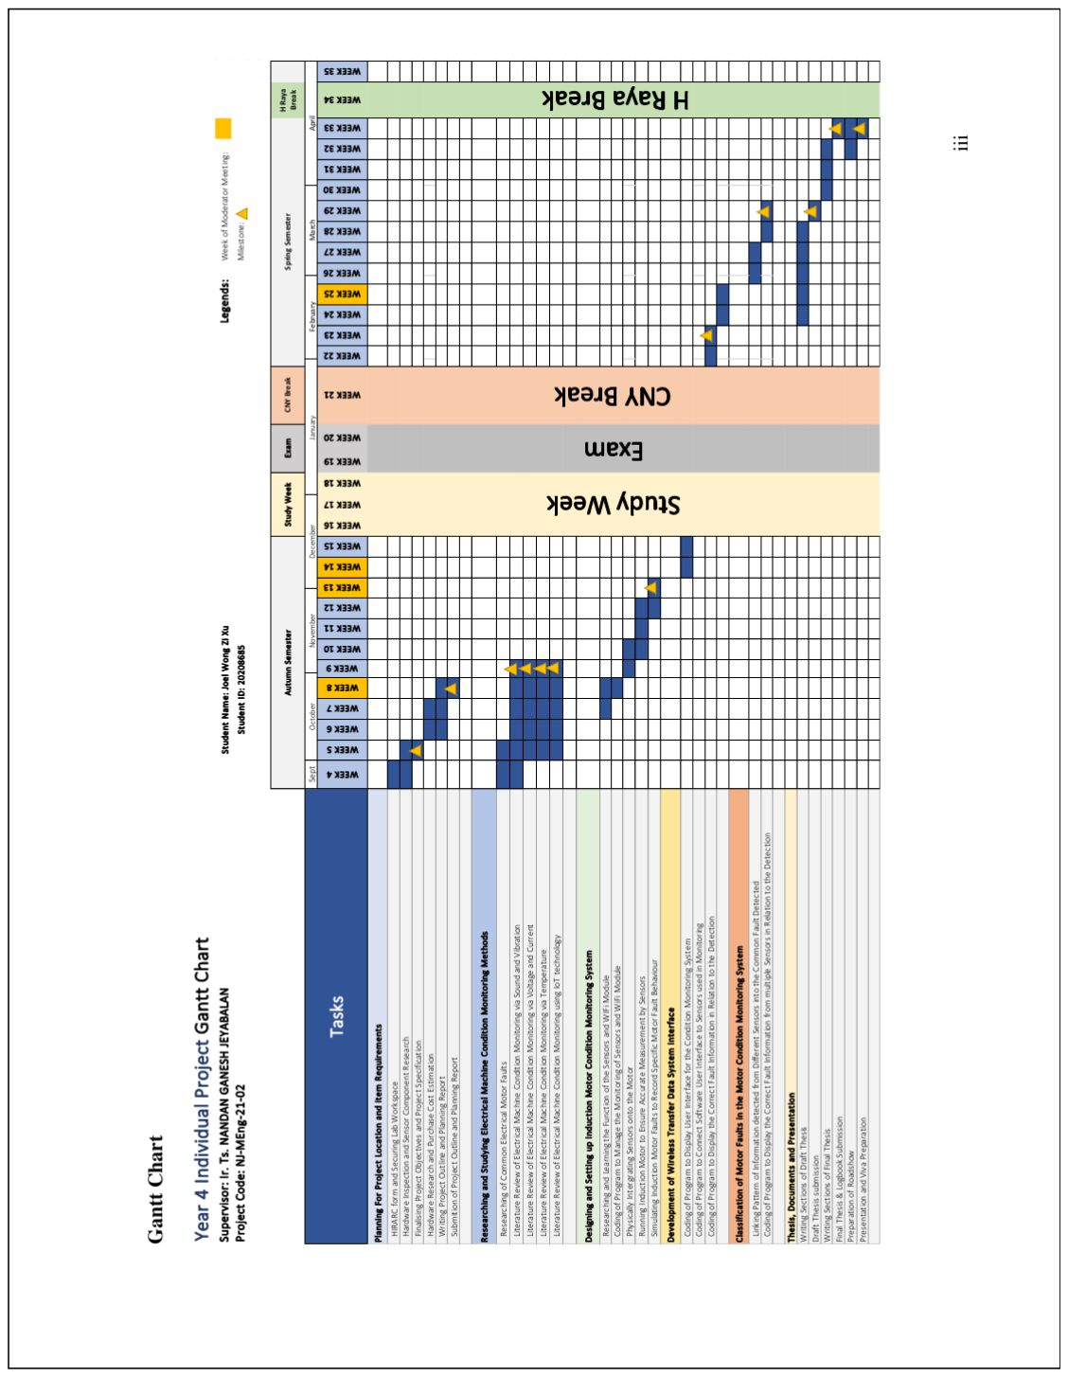
[picture p40: page 29]
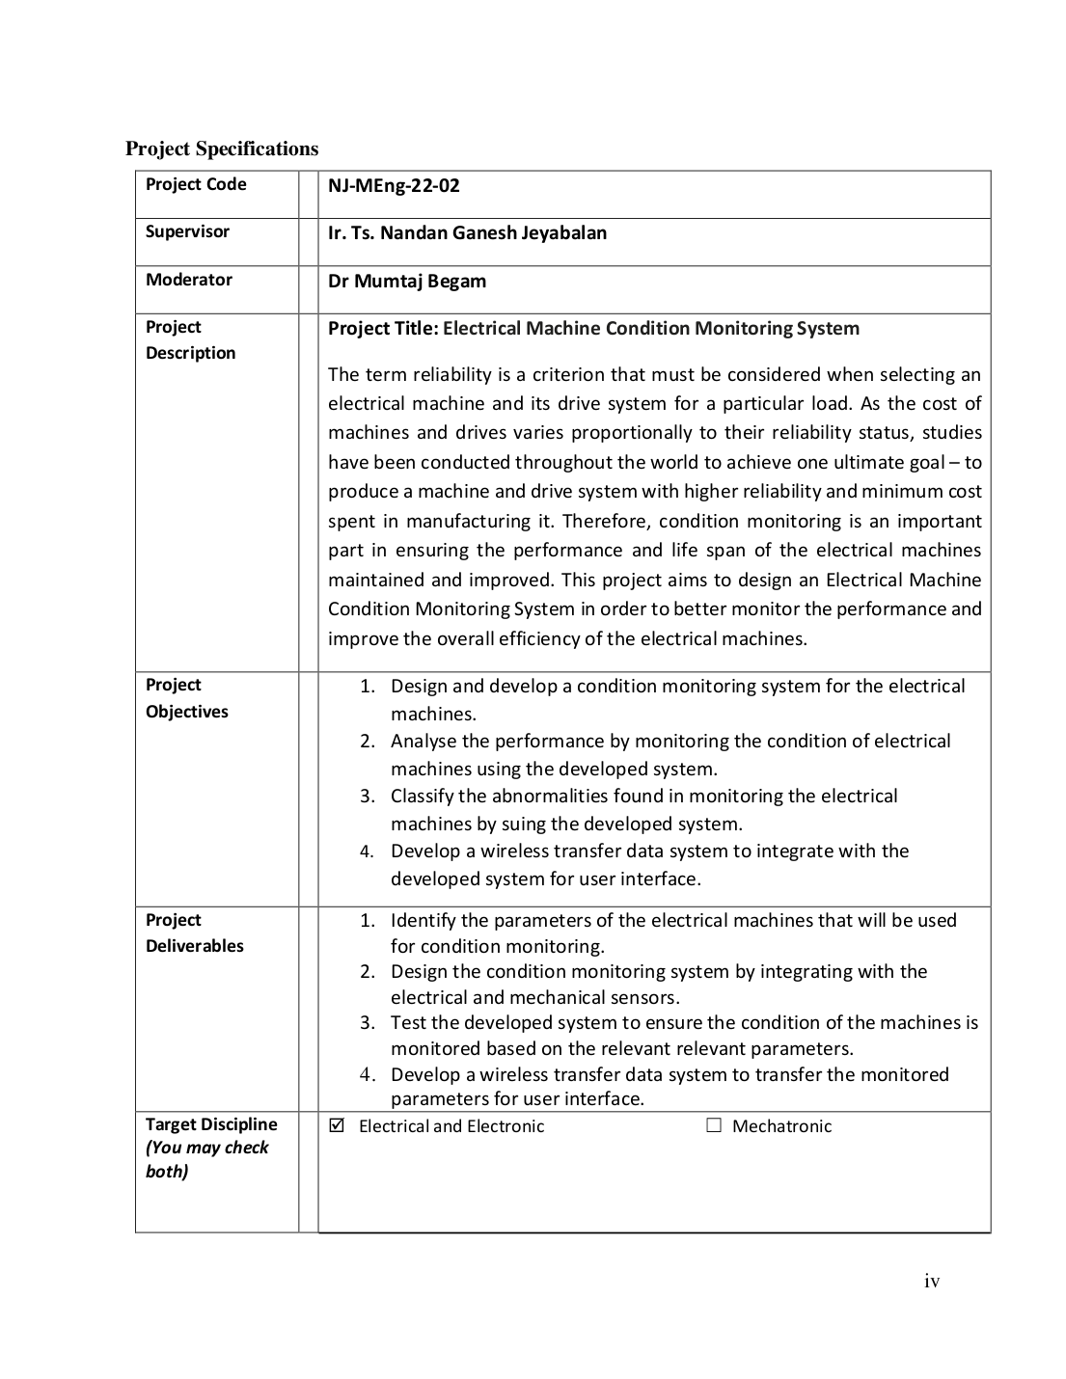
[picture p41: page 30]
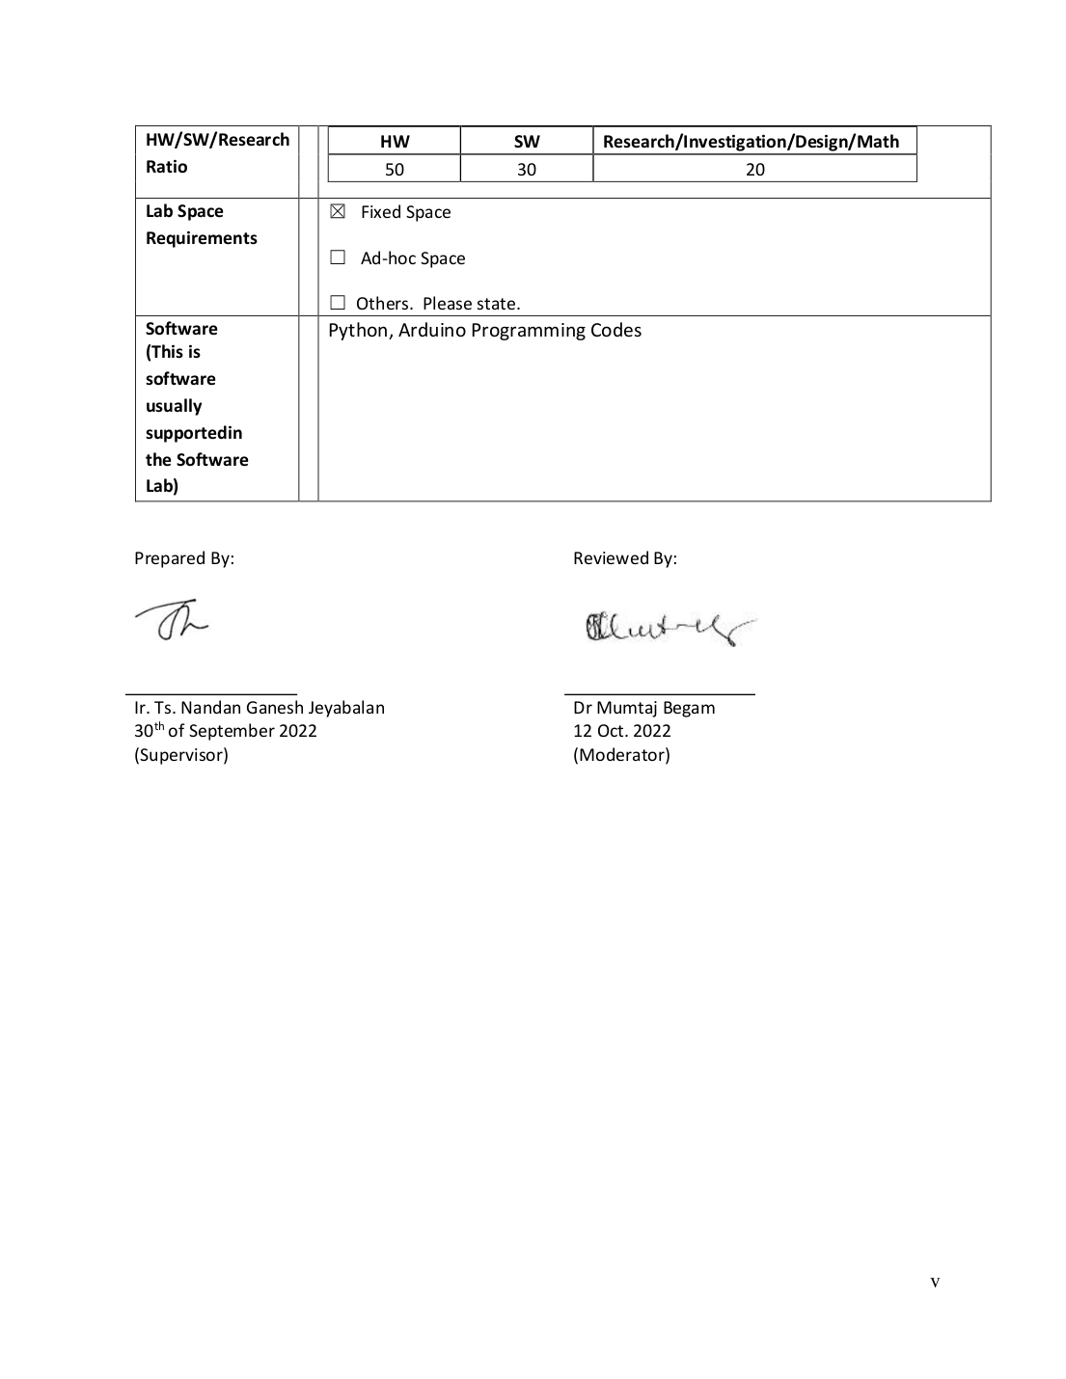
[picture p42: page 31]

8%

## SIMILARITY INDEX

5%

## INTERNET SOURCES

4%

## PUBLICATIONS

6%

## STUDENT PAPERS

1 | 3%
2 | 3%
3 | 1%
4 | <1%
5 | <1%
6 | <1%

# Electrical Machine Condition Monitoring System

ORIGINALITY REPORT

PRIMARY SOURCES

# www.hindawi.com

## Internet Source

# Submitted to University of Nottingham

## Student Paper

# www.coursehero.com

## Internet Source

# Submitted to University Tun Hussein Onn Malaysia

## Student Paper

# "Proceedings of the 13th International Conference on Damage Assessment of Structures"

# , Springer Science and Business Media LLC, 2020

## Publication

Touhami, O., R. Sadoun, A. Belouchrani, S. Hamdani, A. Boukoucha, and S. Ouaged.

# "Remote monitoring system of electrical machines via INTERNET"

# , 2013 9th IEEE International Symposium on Diagnostics for

7 | <1%
8 | <1%
Exclude quotes | Off

### Exclude bibliography On

### Exclude matches Off

# Electric Machines Power Electronics and

Drives (SDEMPED), 2013.

## Publication

# core.ac.uk

## Internet Source

# "Advances in Asset Management and Condition Monitoring"

# , Springer Science and Business Media LLC, 2020

## Publication
