xian-cong/Final-Year-Project-Nottingham/links and documents/progress review meeting/progress review.pdf

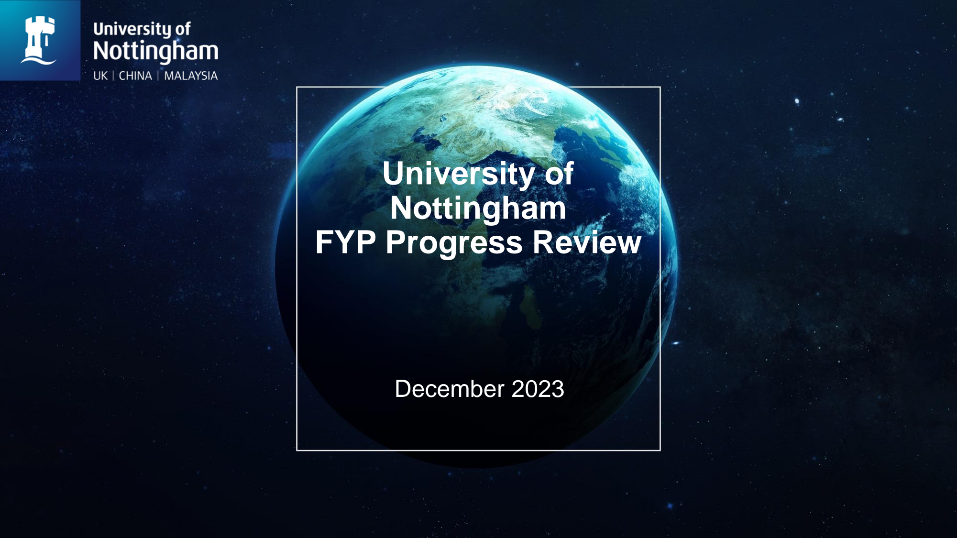
[picture p43: page 1]

# University of Nottingham FYP Progress Review

## December 2023

# Gantt Chart

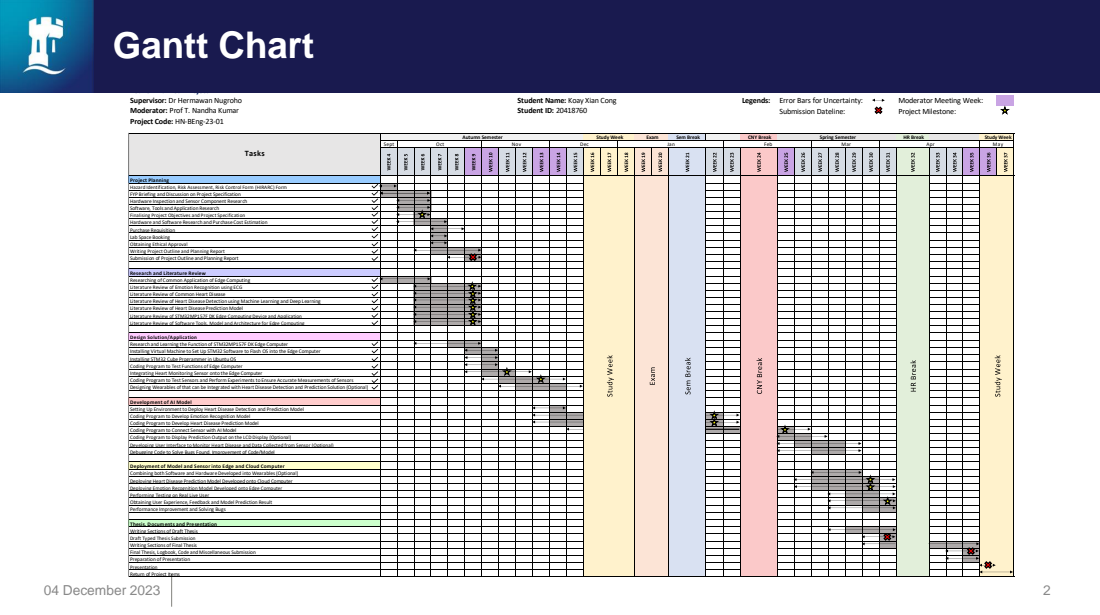
[picture p44: page 2]
04 December 2023

# Setting Up STM32CubeIDE & Testing Code

## Requirements

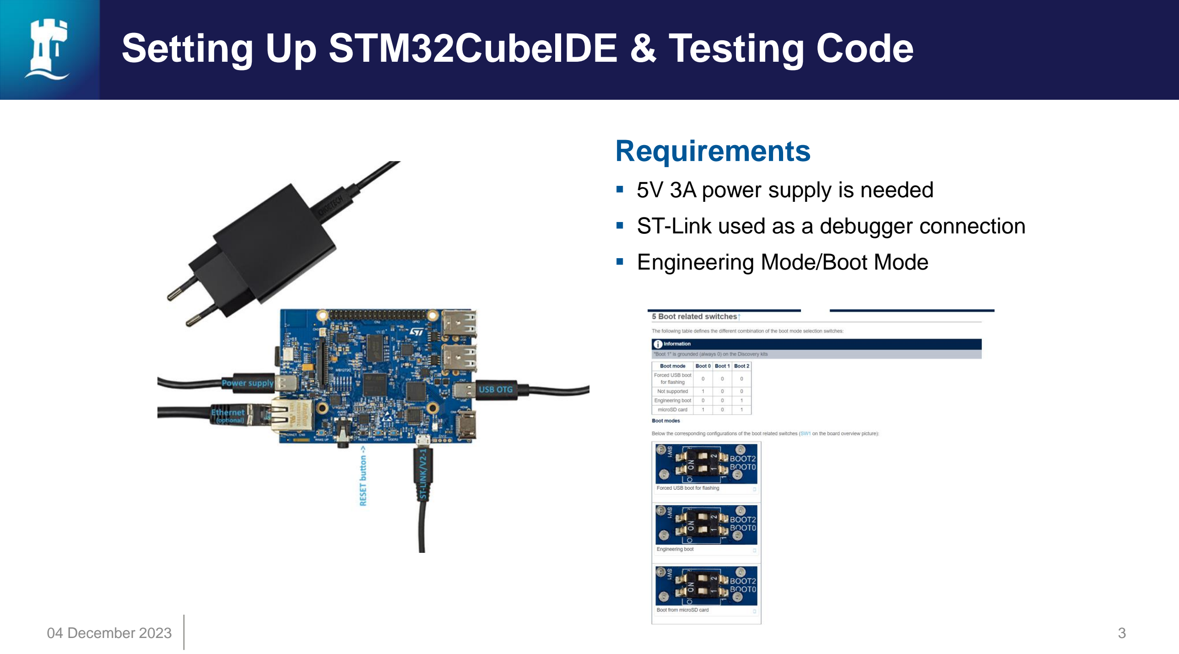
[picture p45: page 3]

- 5V 3A power supply is needed
- ST-Link used as a debugger connection
- Engineering Mode/Boot Mode

# Setting Up STM32CubeIDE & Testing Code

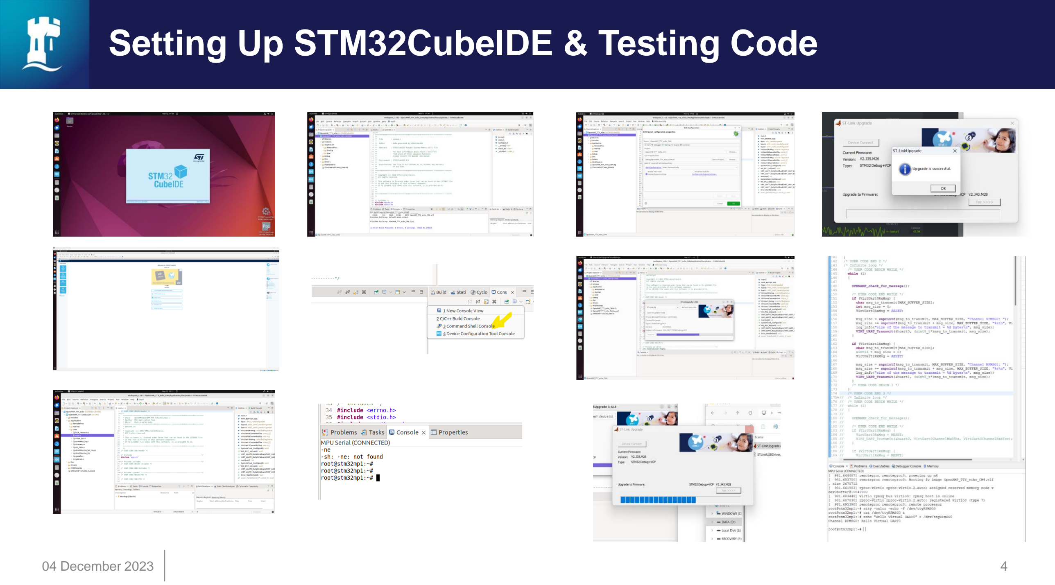
[picture p46: page 4]

# Connecting ECG sensors onto STM32MP157F-DK2

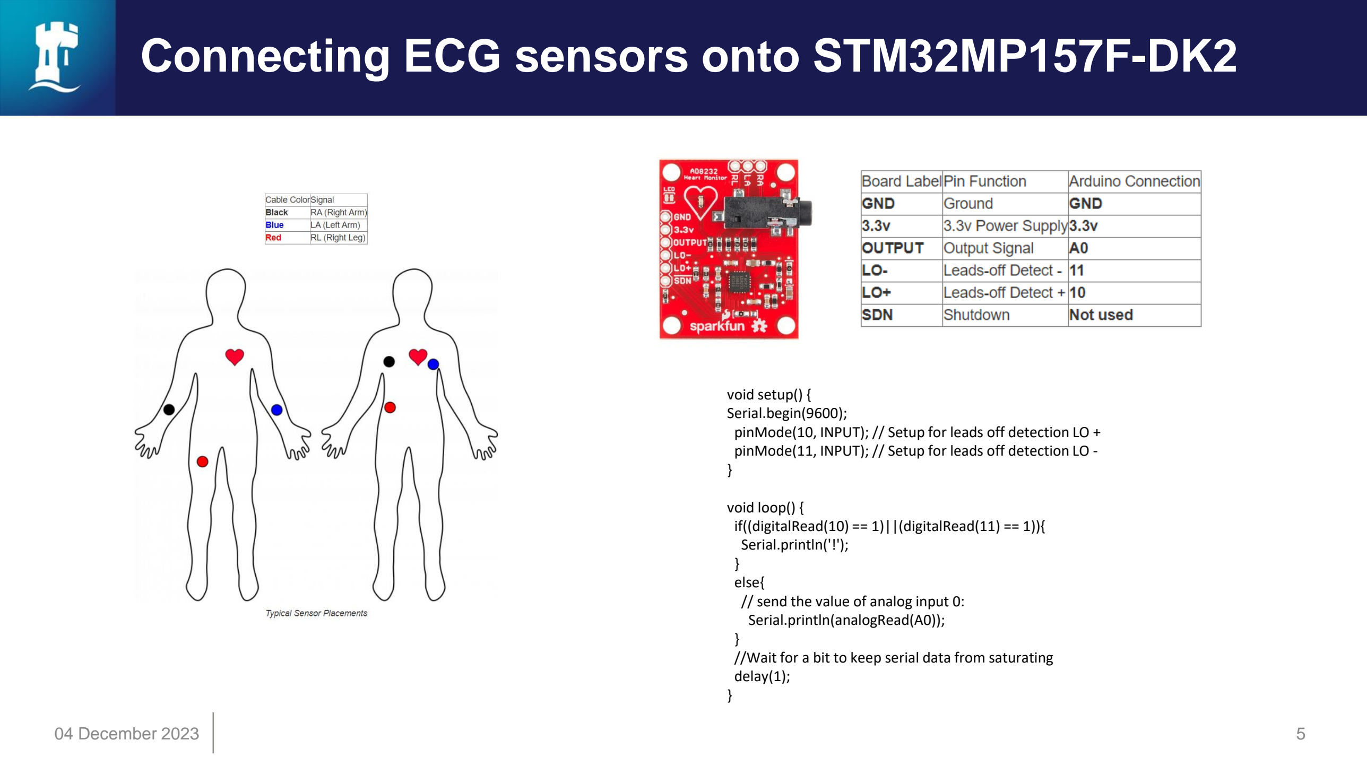
[picture p47: page 5]

void setup() {
Serial.begin(9600);
pinMode(10, INPUT); // Setup for leads off detection LO + pinMode(11, INPUT); // Setup for leads off detection LO -}

void loop() {
if((digitalRead(10) == 1)||(digitalRead(11) == 1)){ Serial.println('!');
}
else{
// send the value of analog input 0: Serial.println(analogRead(A0));
}
//Wait for a bit to keep serial data from saturating delay(1);
}

# Connecting ECG sensors onto STM32MP157F-DK2

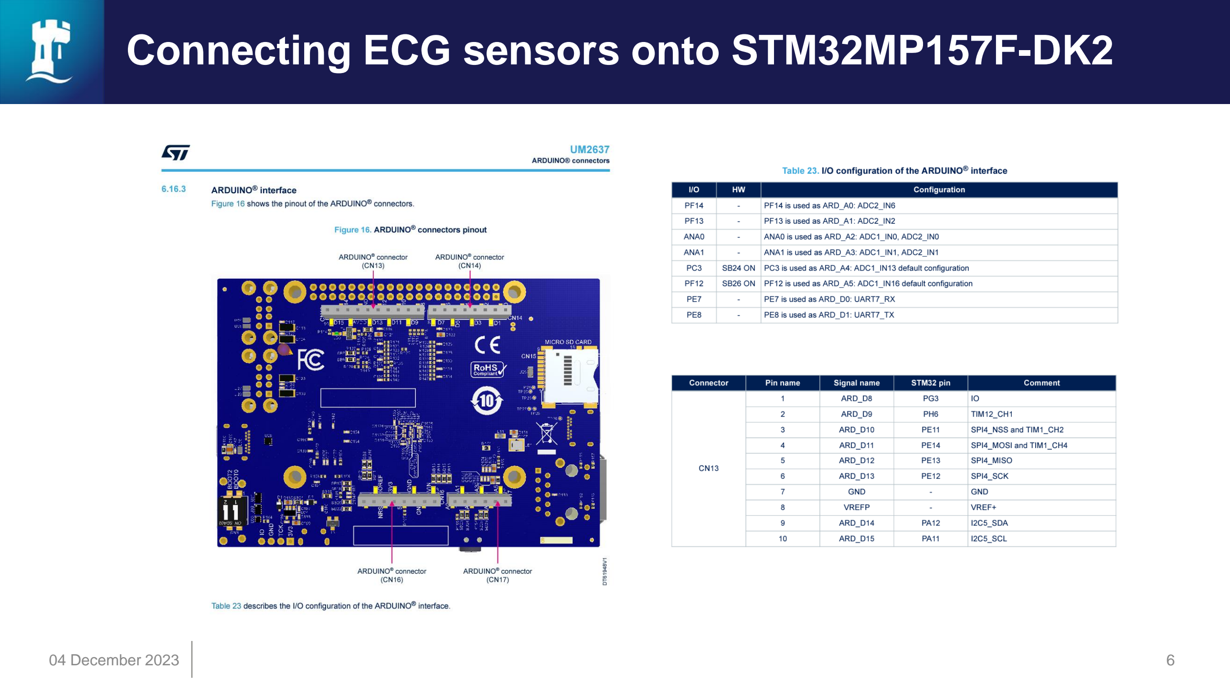
[picture p48: page 6]

# Problems

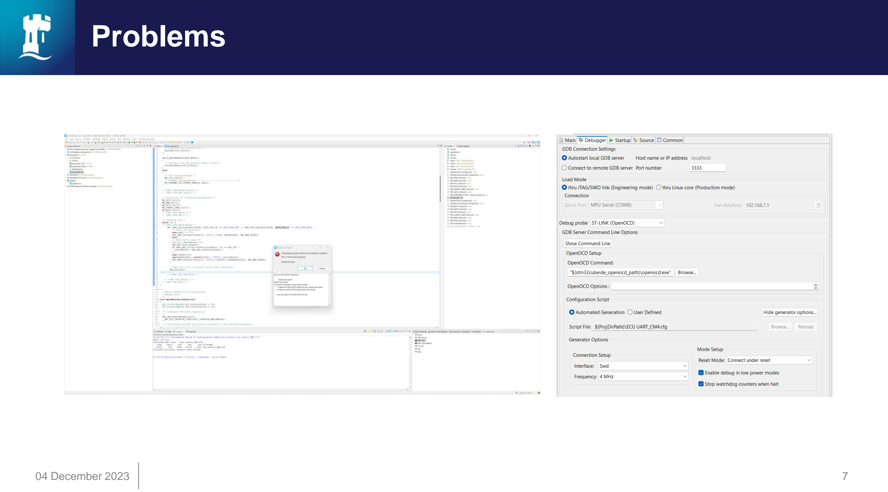
[picture p49: page 7]

# STM32 Pin Configuration

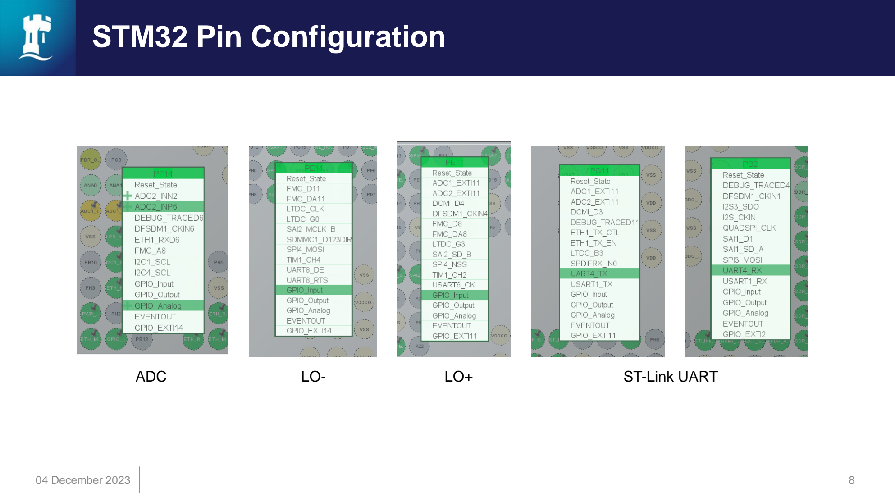
[picture p50: page 8]

ADC | LO- | LO+ | ST-Link UART

# ADC

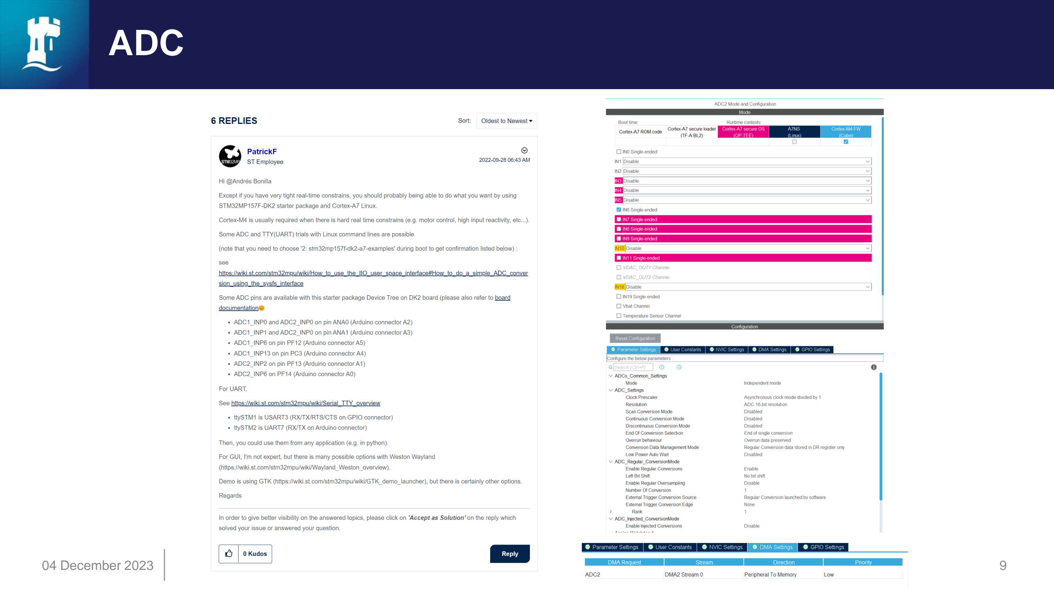
[picture p51: page 9]

# Problem

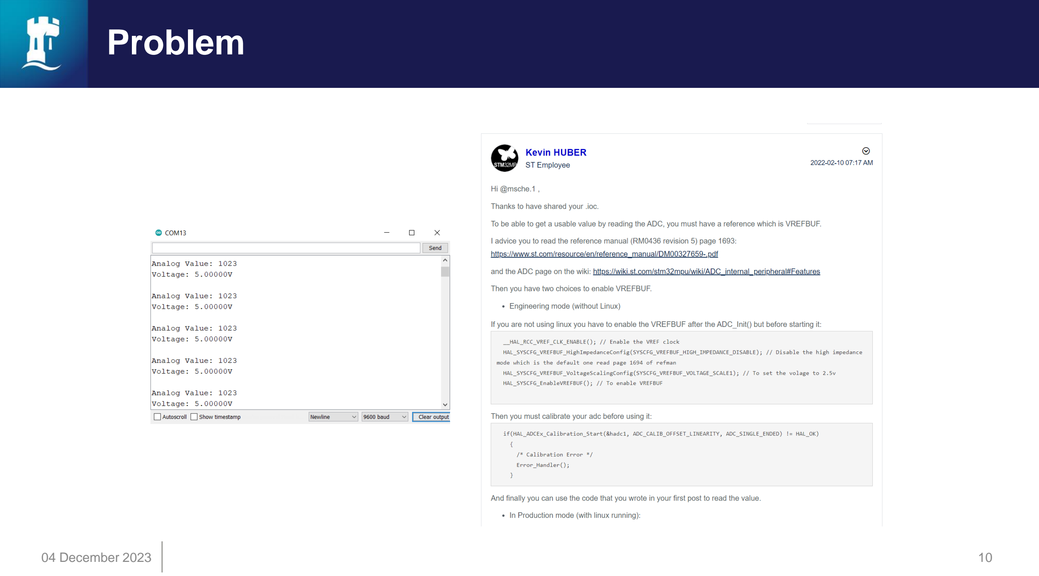
[picture p52: page 10]

# UART

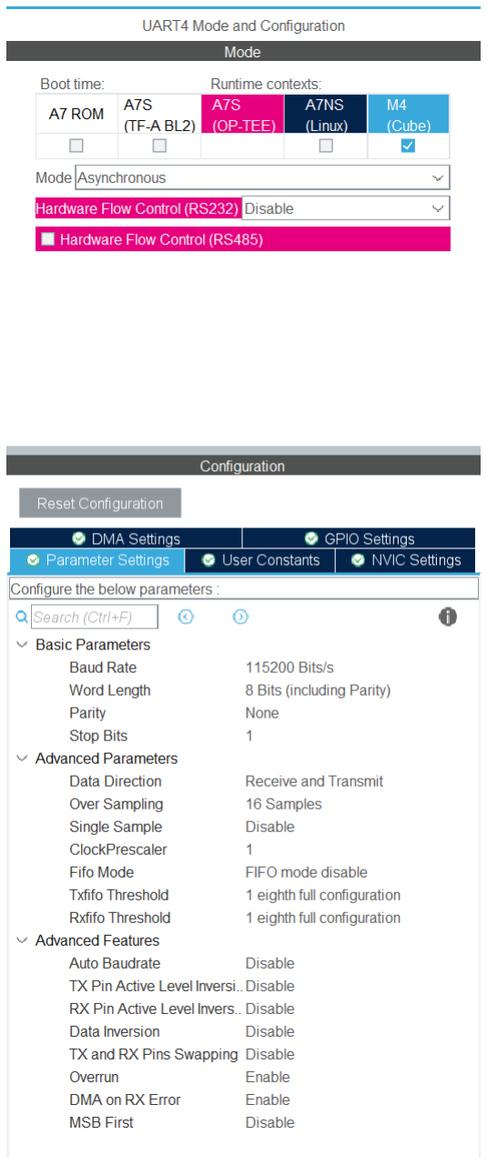
[picture p53: figure]

# Problems

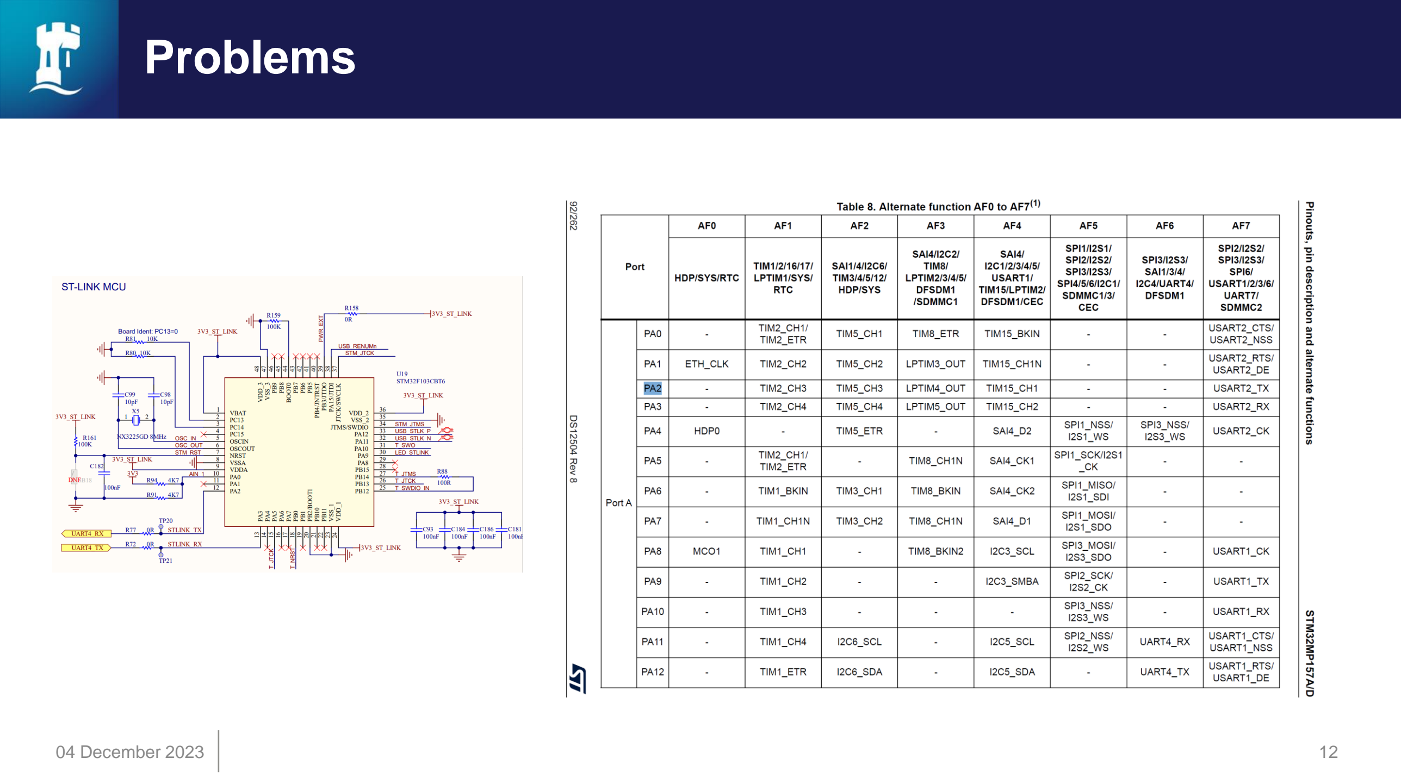
[picture p54: page 12]

# Problems

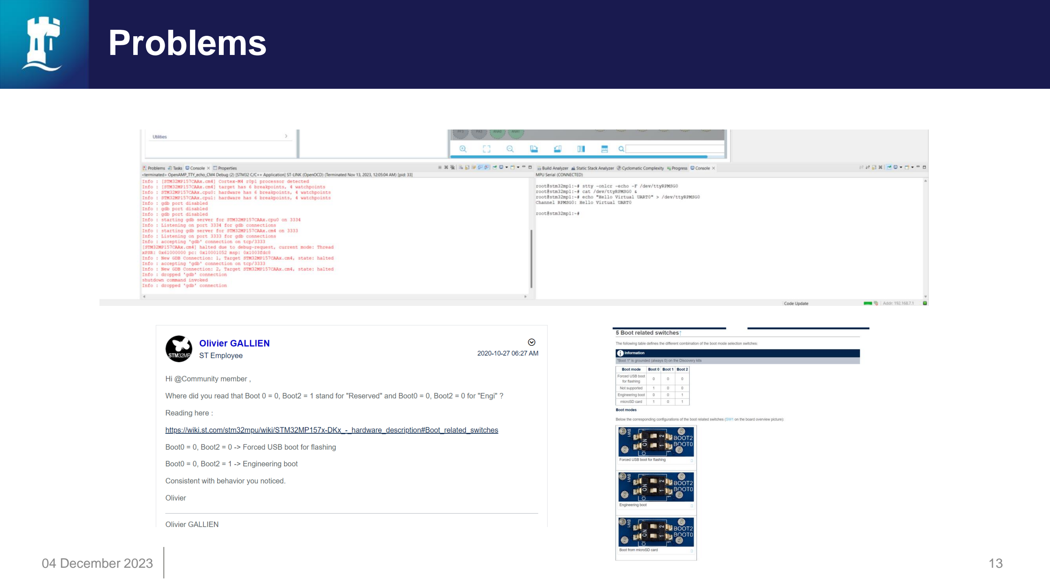
[picture p55: page 13]

# Code – Printing ADC values via ST-Link

while (1)
{
HAL_ADC_Start(&hadc2);
HAL_ADC_PollForConversion(&hadc2, HAL_MAX_DELAY); raw = HAL_ADC_GetValue(&hadc2);
HAL_Delay(10);
sprintf(msg, "%d\r\n", raw);
HAL_UART_Transmit(&huart4, msg, strlen(msg), HAL_MAX_DELAY); }

# Code – Printing ADC values via ST-Link

__HAL_RCC_VREF_CLK_ENABLE(); // Enable the VREF clock HAL_SYSCFG_VREFBUF_HighImpedanceConfig(SYSCFG_VREFBUF_HIGH_IMPEDANC E_DISABLE); // Disable the high impedance mode which is the default one read page 1694 of refman HAL_SYSCFG_VREFBUF_VoltageScalingConfig(SYSCFG_VREFBUF_VOLTAGE_SCAL E1); // To set the volage to 2.5v
HAL_SYSCFG_EnableVREFBUF(); // To enable VREFBUF

if(HAL_ADCEx_Calibration_Start(&hadc2, ADC_CALIB_OFFSET_LINEARITY, ADC_SINGLE_ENDED) != HAL_OK)
{
/* Calibration Error */
Error_Handler();
}

# Result

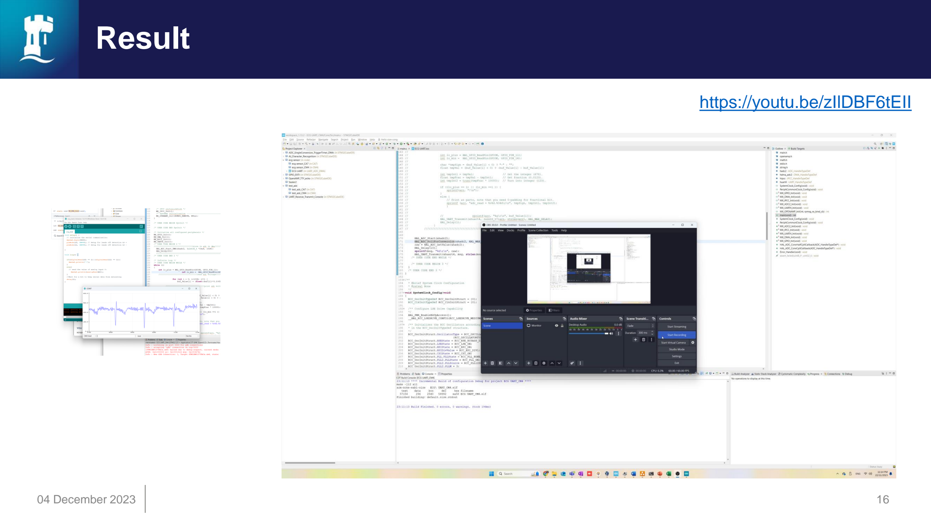
[picture p56: page 16]

https://youtu.be/zIlDBF6tEII

# Wearable Design – Reference

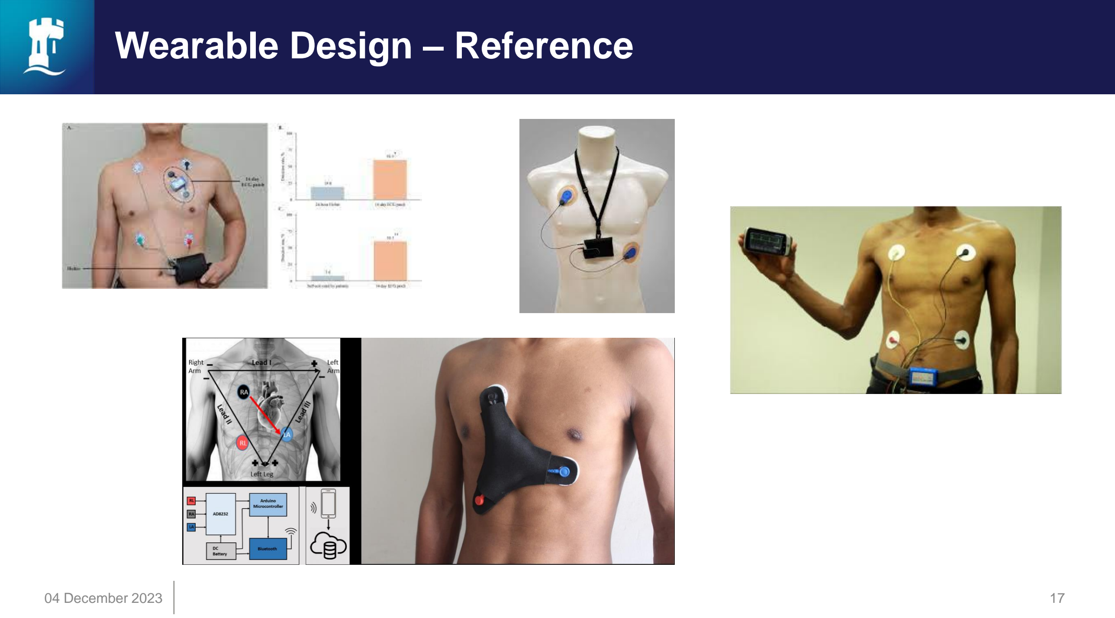
[picture p57: page 17]

# Wearable Design – Clip on Pants

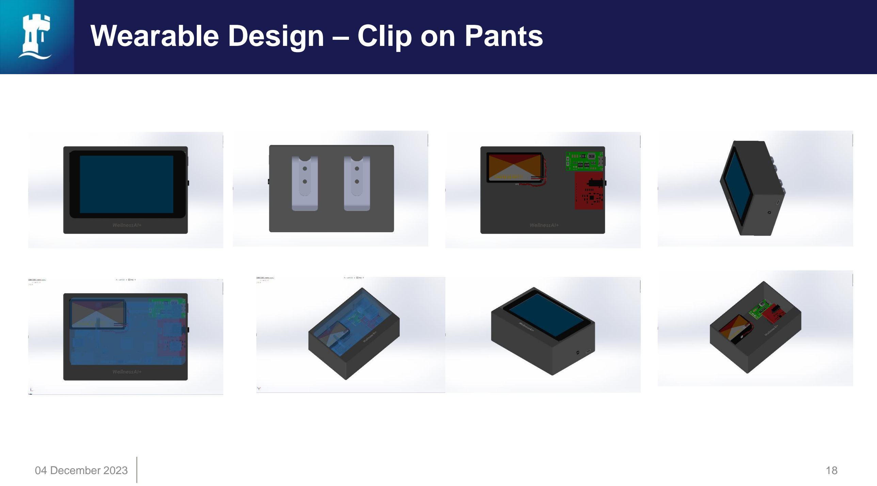
[picture p58: page 18]

# Gantt Chart – What’s Next?

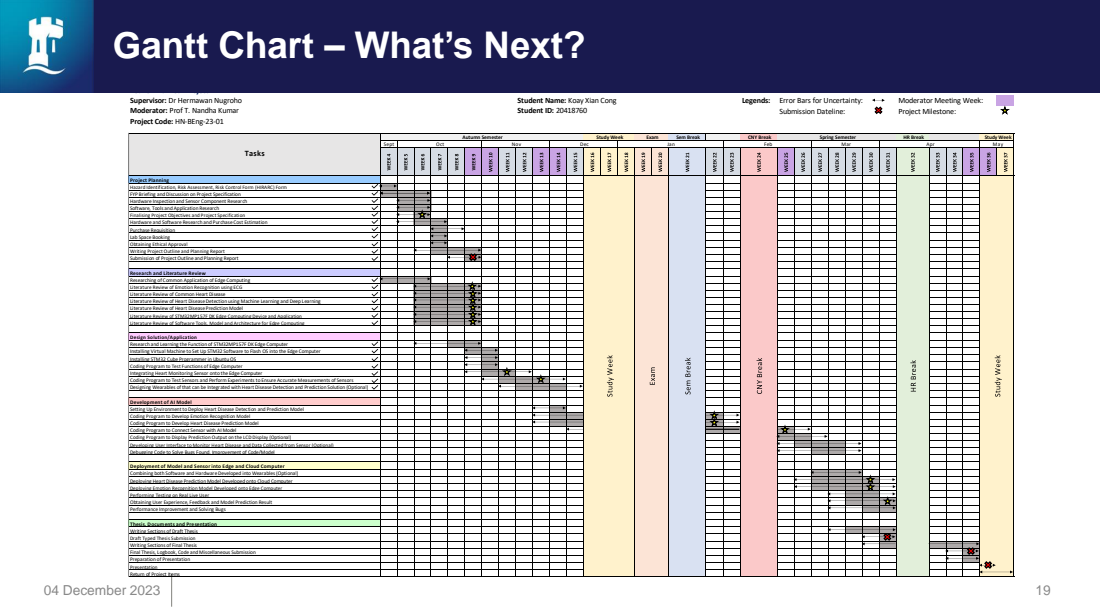
[picture p59: page 19]

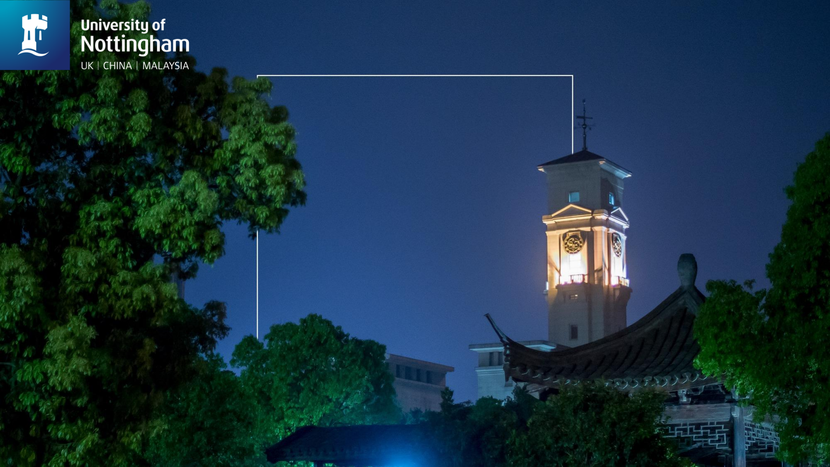
[picture p60: page 20]
