xian-cong/Final-Year-Project-Nottingham/links and documents/progress review meeting/progress review 1.pdf

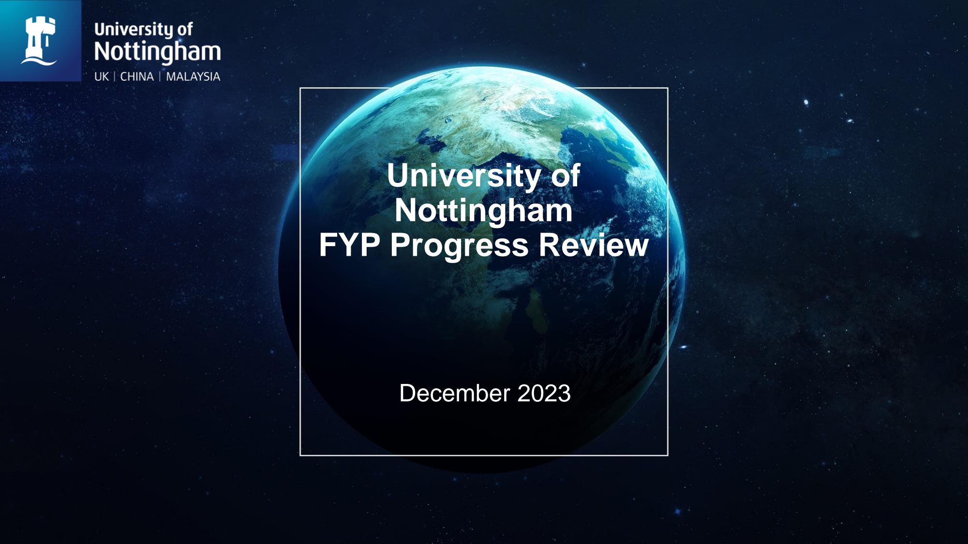
[picture p61: page 1]

# University of Nottingham FYP Progress Review

## December 2023

# Setting Up STM32CubeIDE & Testing Code

## Requirements

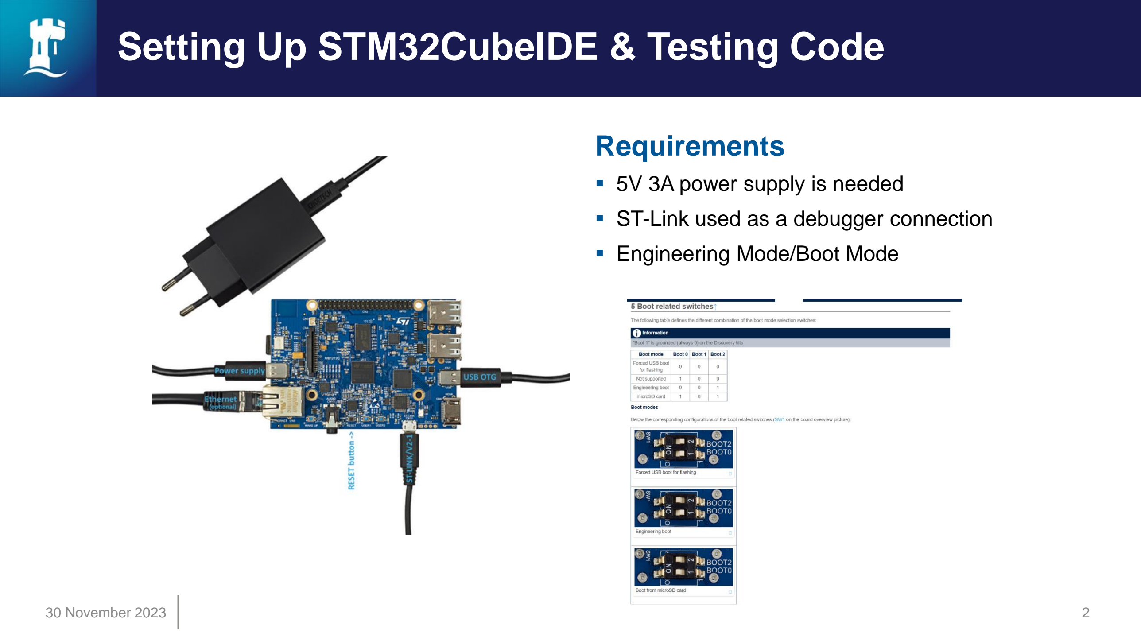
[picture p62: page 2]

30 November 2023 | 2
- 5V 3A power supply is needed
- ST-Link used as a debugger connection
- Engineering Mode/Boot Mode

# Setting Up STM32CubeIDE & Testing Code

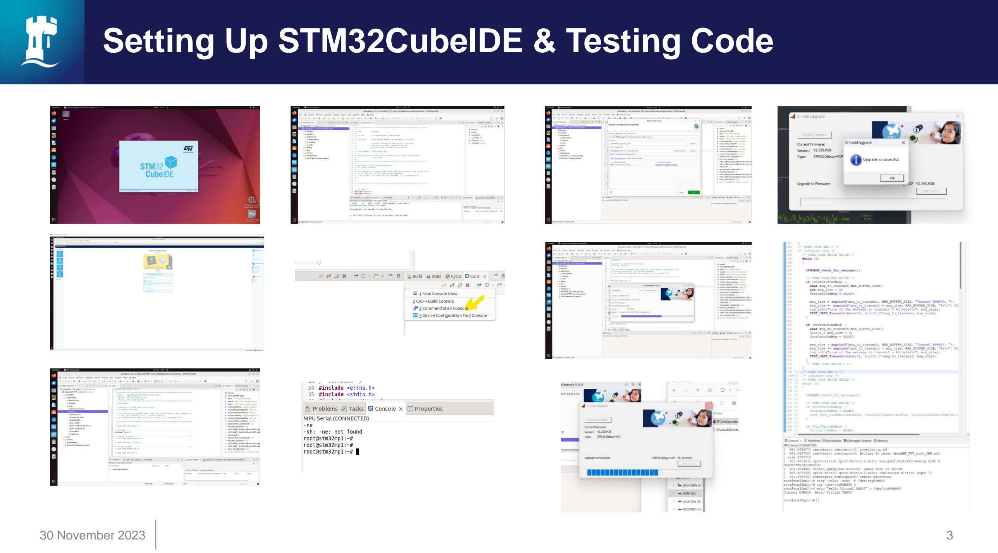
[picture p63: page 3]

# Connecting ECG sensors onto STM32MP157F-DK2

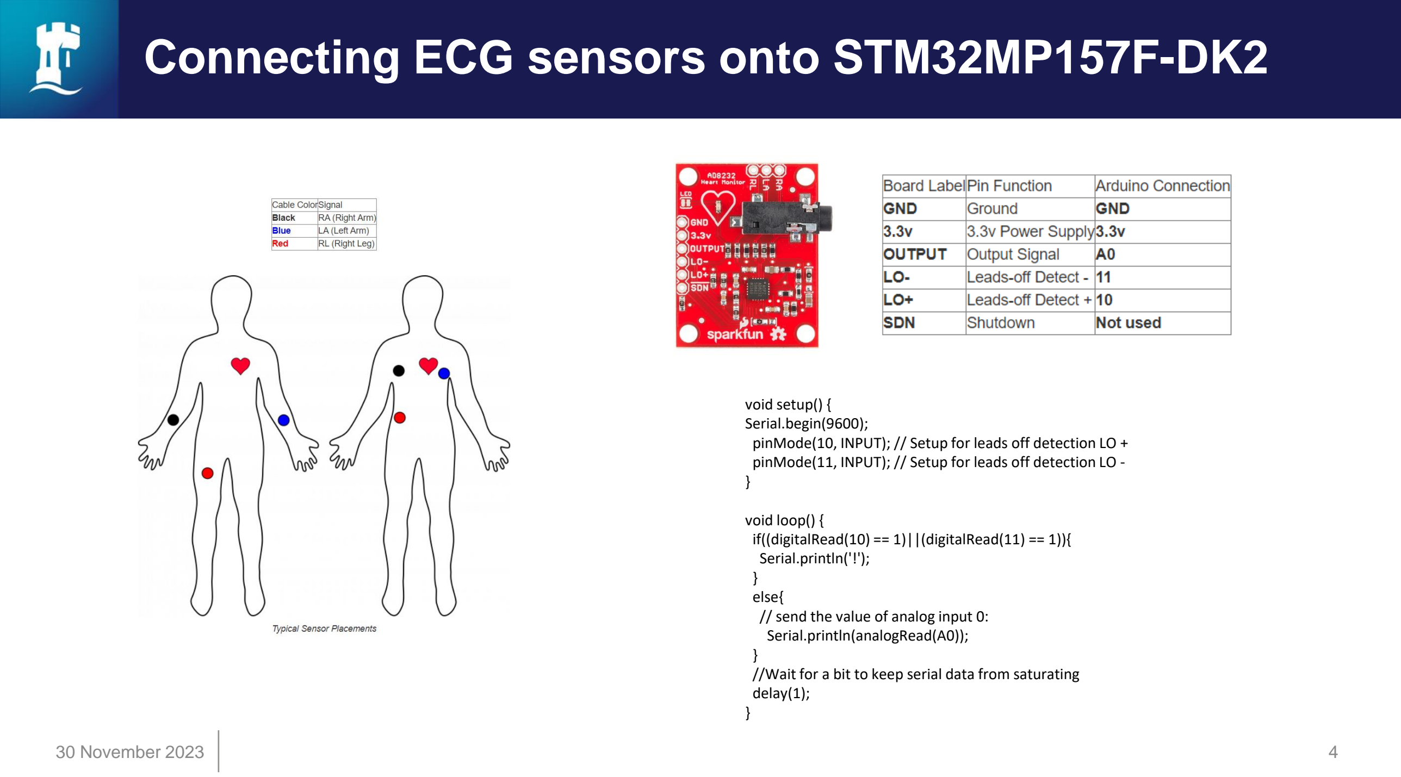
[picture p64: page 4]

void setup() {
Serial.begin(9600);
pinMode(10, INPUT); // Setup for leads off detection LO + pinMode(11, INPUT); // Setup for leads off detection LO -}

void loop() {
if((digitalRead(10) == 1)||(digitalRead(11) == 1)){ Serial.println('!');
}
else{
// send the value of analog input 0: Serial.println(analogRead(A0));
}
//Wait for a bit to keep serial data from saturating delay(1);
}

# Connecting ECG sensors onto STM32MP157F-DK2

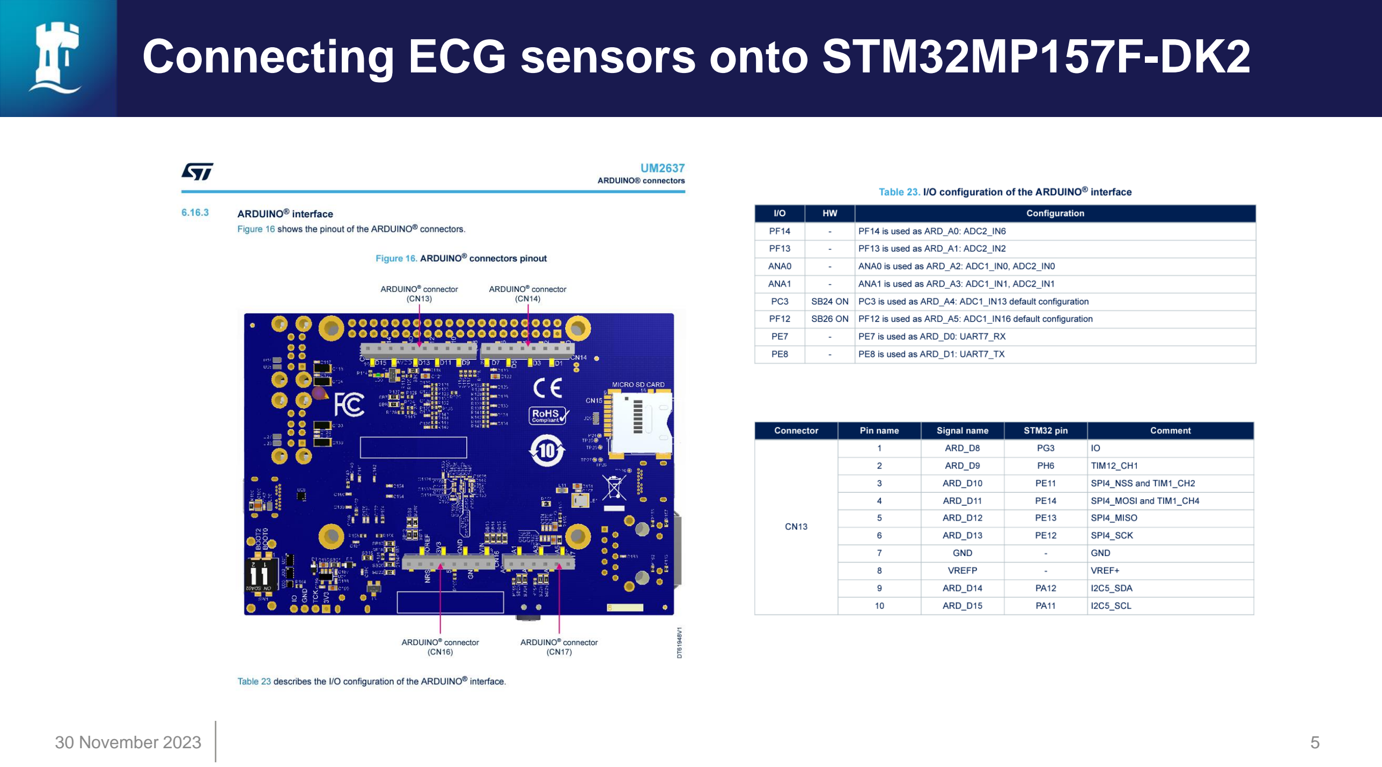
[picture p65: page 5]

# Problems

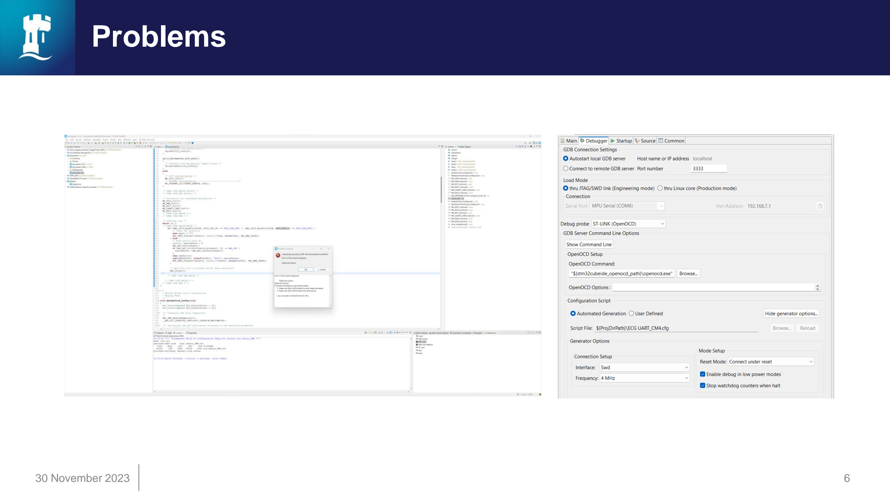
[picture p66: page 6]

# STM32 Pin Configuration

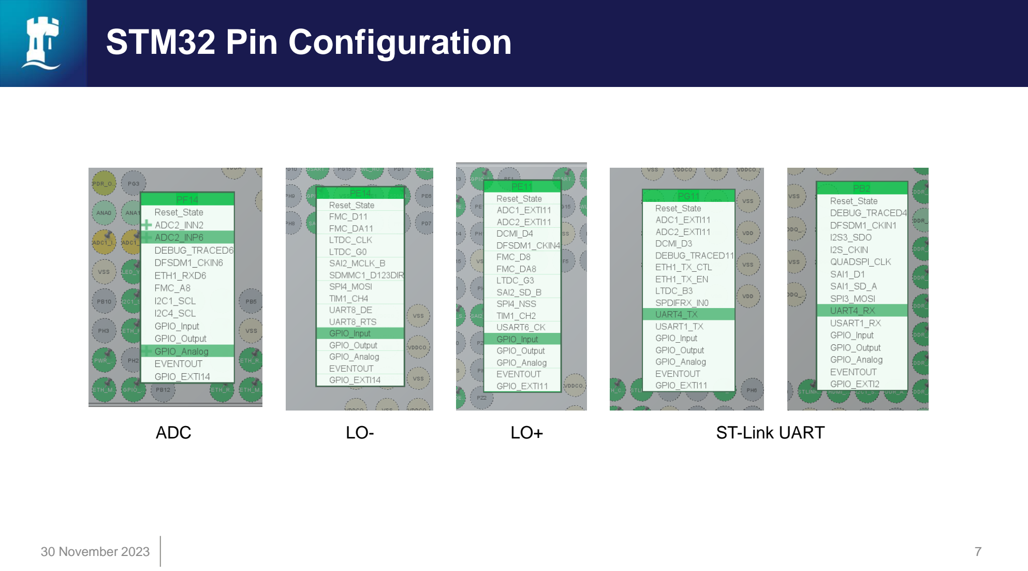
[picture p67: page 7]

ADC | LO- | LO+ | ST-Link UART

# ADC

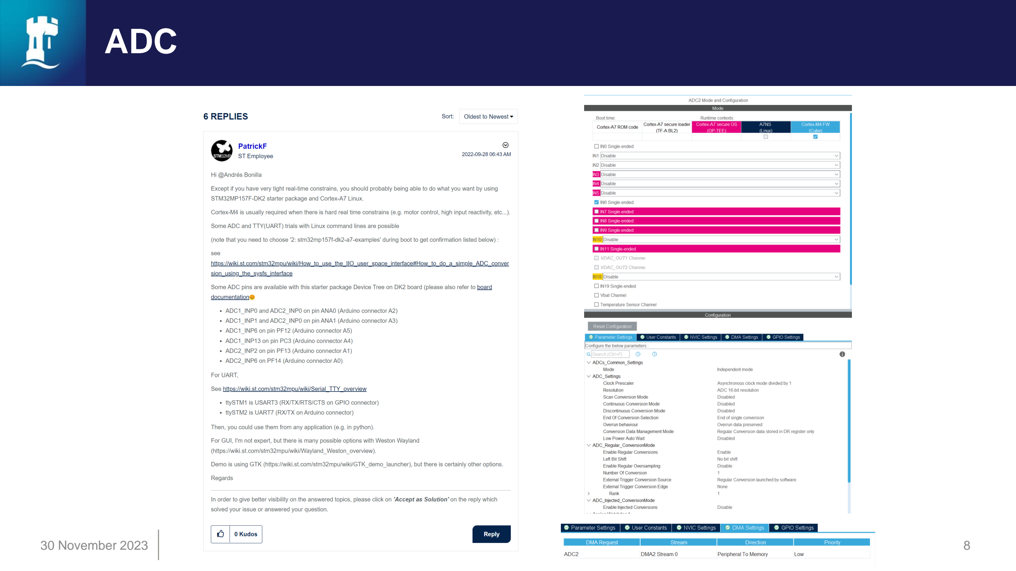
[picture p68: page 8]

# Problem

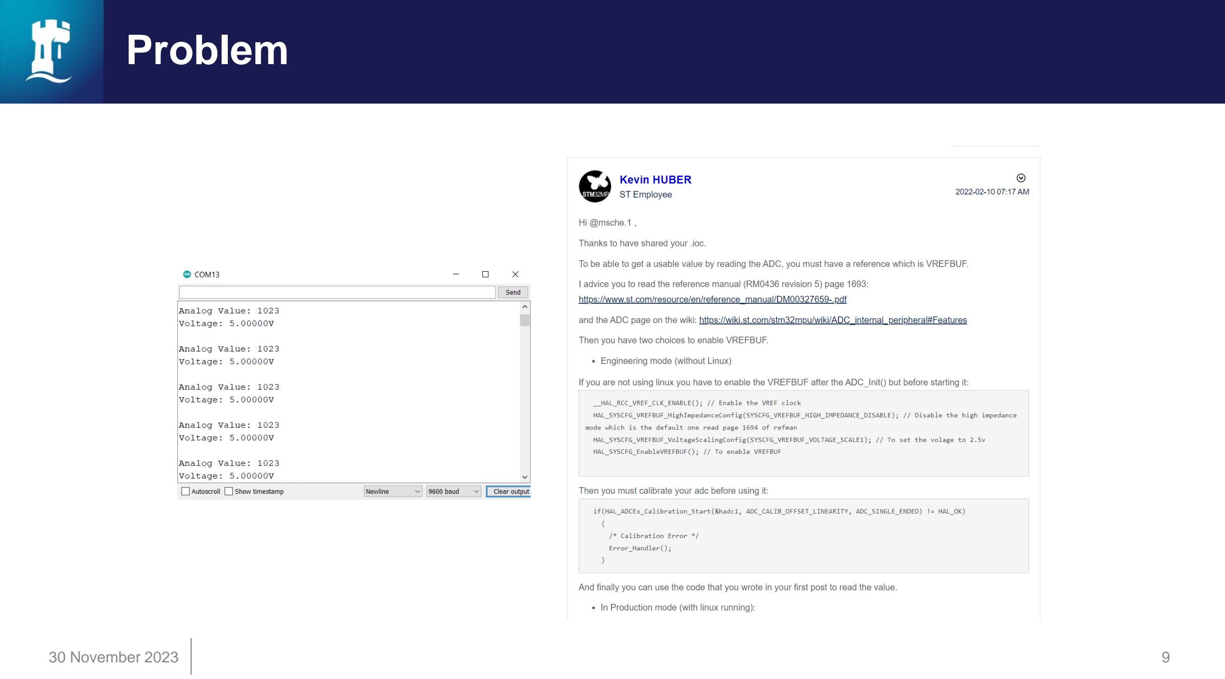
[picture p69: page 9]

# UART


# Problems

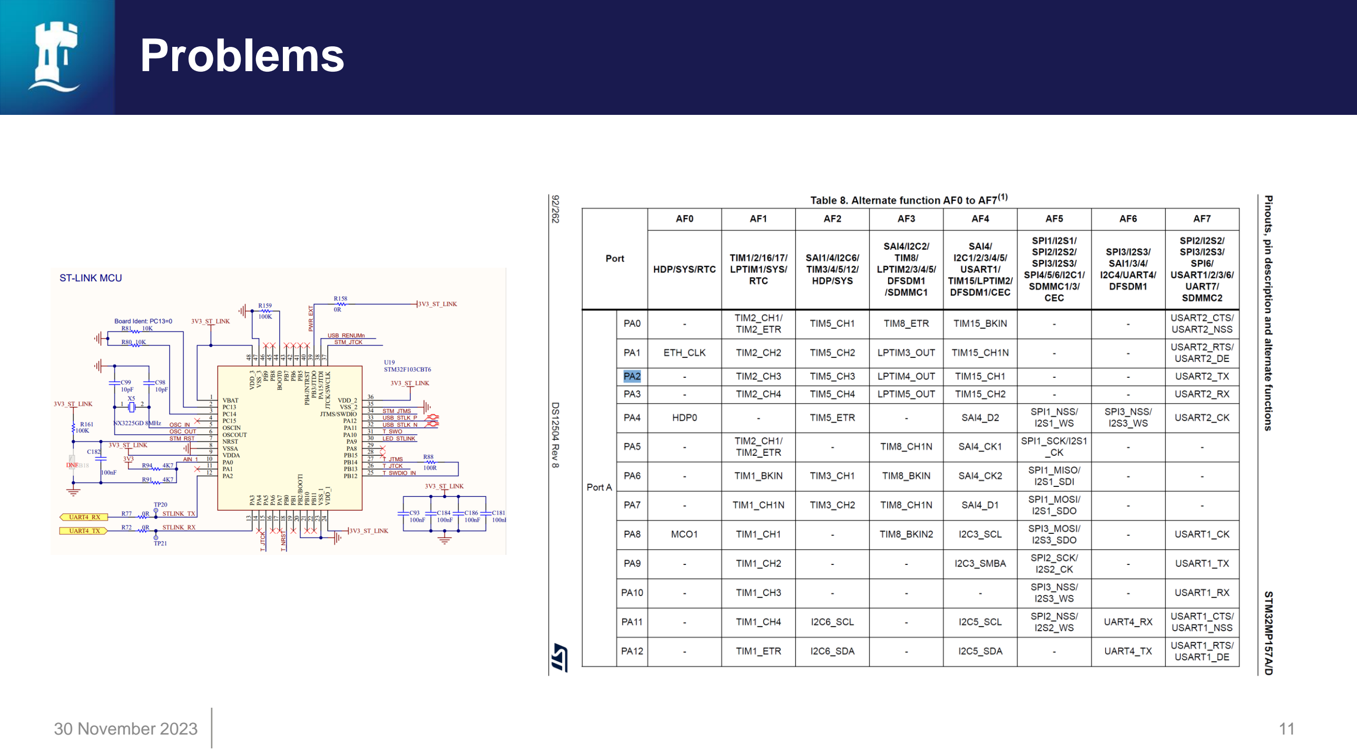
[picture p70: page 11]

# Problems

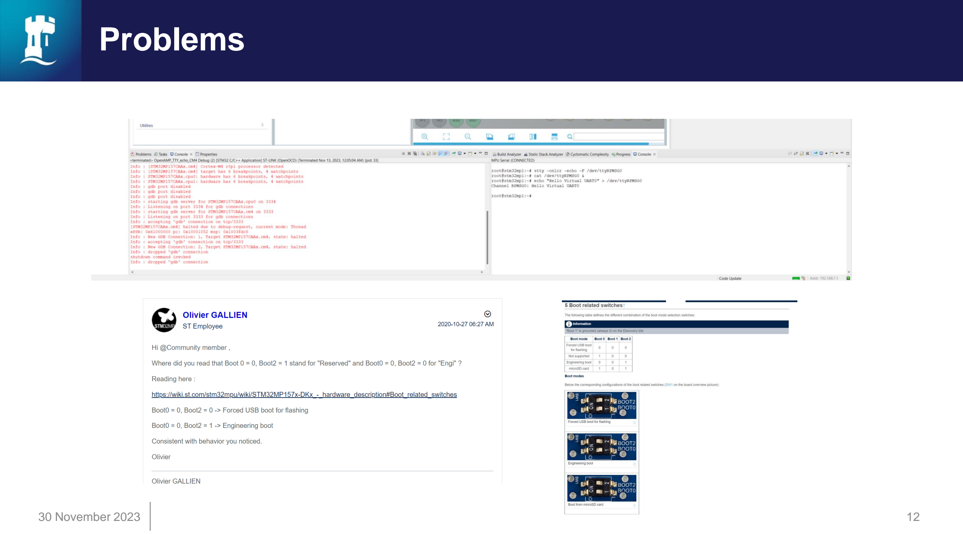
[picture p71: page 12]

# Code – Printing ADC values via ST-Link

while (1)
{
HAL_ADC_Start(&hadc2);
HAL_ADC_PollForConversion(&hadc2, HAL_MAX_DELAY); raw = HAL_ADC_GetValue(&hadc2);
HAL_Delay(10);
sprintf(msg, "%d\r\n", raw);
HAL_UART_Transmit(&huart4, msg, strlen(msg), HAL_MAX_DELAY); }

# Code – Printing ADC values via ST-Link

__HAL_RCC_VREF_CLK_ENABLE(); // Enable the VREF clock HAL_SYSCFG_VREFBUF_HighImpedanceConfig(SYSCFG_VREFBUF_HIGH_IMPEDANC E_DISABLE); // Disable the high impedance mode which is the default one read page 1694 of refman HAL_SYSCFG_VREFBUF_VoltageScalingConfig(SYSCFG_VREFBUF_VOLTAGE_SCAL E1); // To set the volage to 2.5v
HAL_SYSCFG_EnableVREFBUF(); // To enable VREFBUF

if(HAL_ADCEx_Calibration_Start(&hadc2, ADC_CALIB_OFFSET_LINEARITY, ADC_SINGLE_ENDED) != HAL_OK)
{
/* Calibration Error */
Error_Handler();
}

# Result

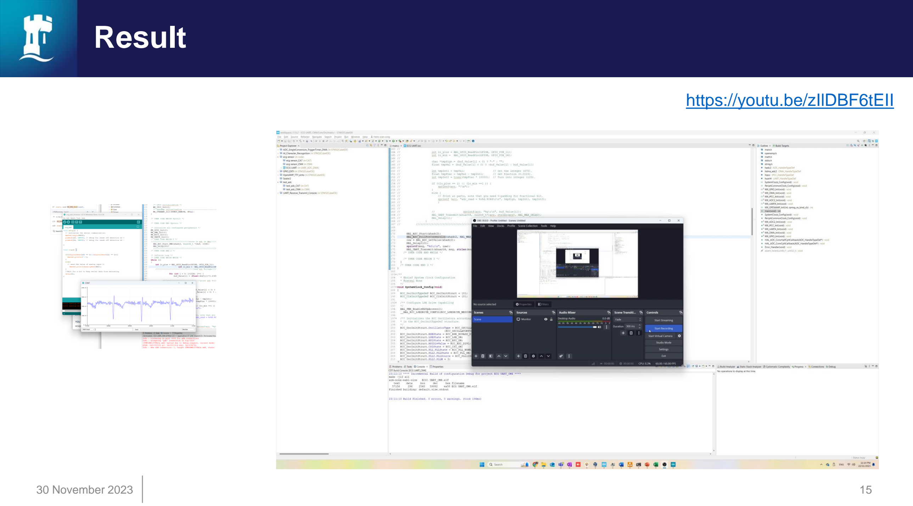
[picture p72: page 15]

https://youtu.be/zIlDBF6tEII

# Wearable Design – Reference

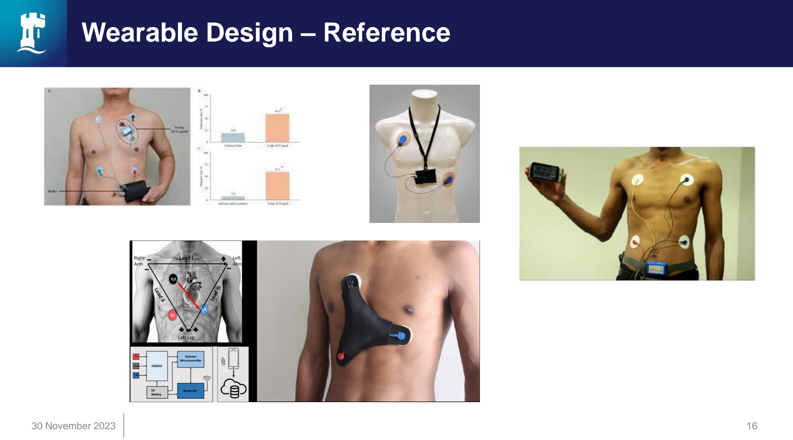
[picture p73: page 16]

# Wearable Design – Clip on Pants

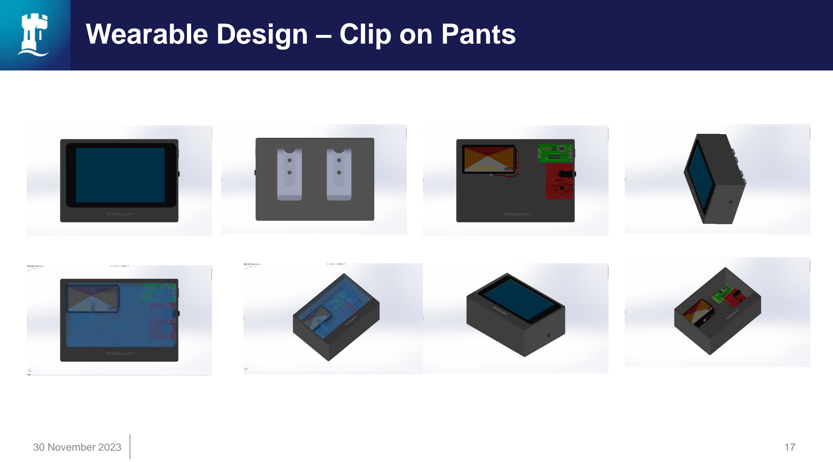
[picture p74: page 17]
