xian-cong/Final-Year-Project-Nottingham/links and documents/defense interview/Additional.pdf

## ARM Cortex-M

Original idea of the project (wearables):
Proof that ARM Cortex-M chips can run AI -

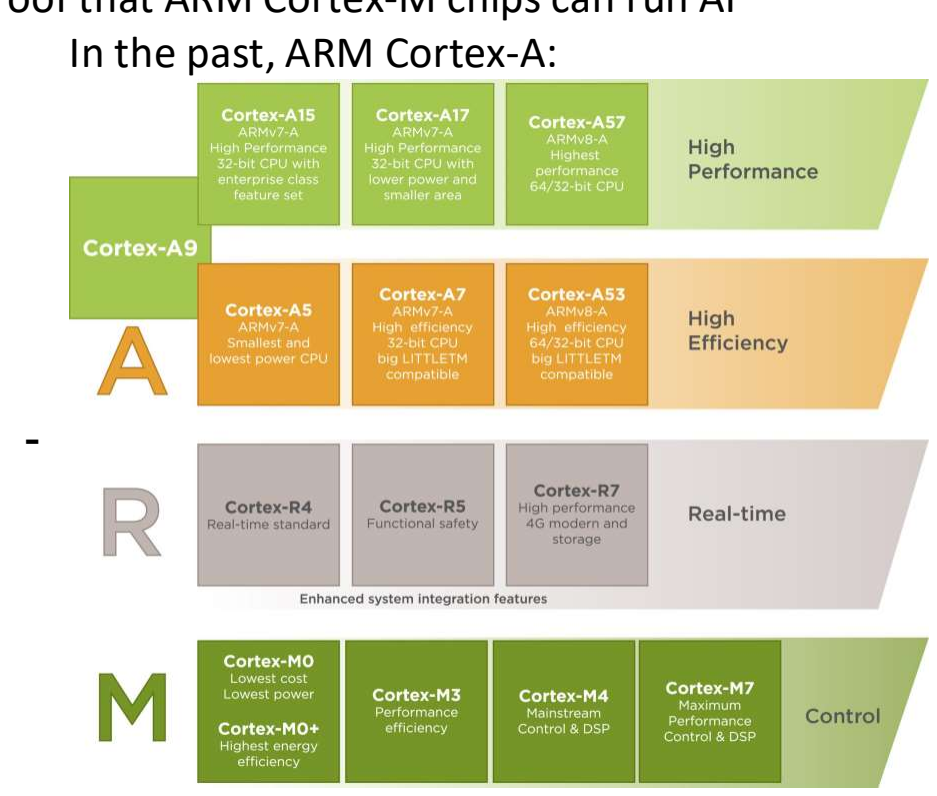
[picture p75: figure]
In the past, ARM Cortex-A: -

Ultra-low power

# - DSP

- https://www.linkedin.com/pulse/arm-cortex-m4-embedded-systems-exploring/ Demo: https://wiki.st.com/stm32mpu/wiki/Getting_started/STM32MP1_boards/STM32MP157x-DK2/Let%27s_start/Use_the_demo_launcher

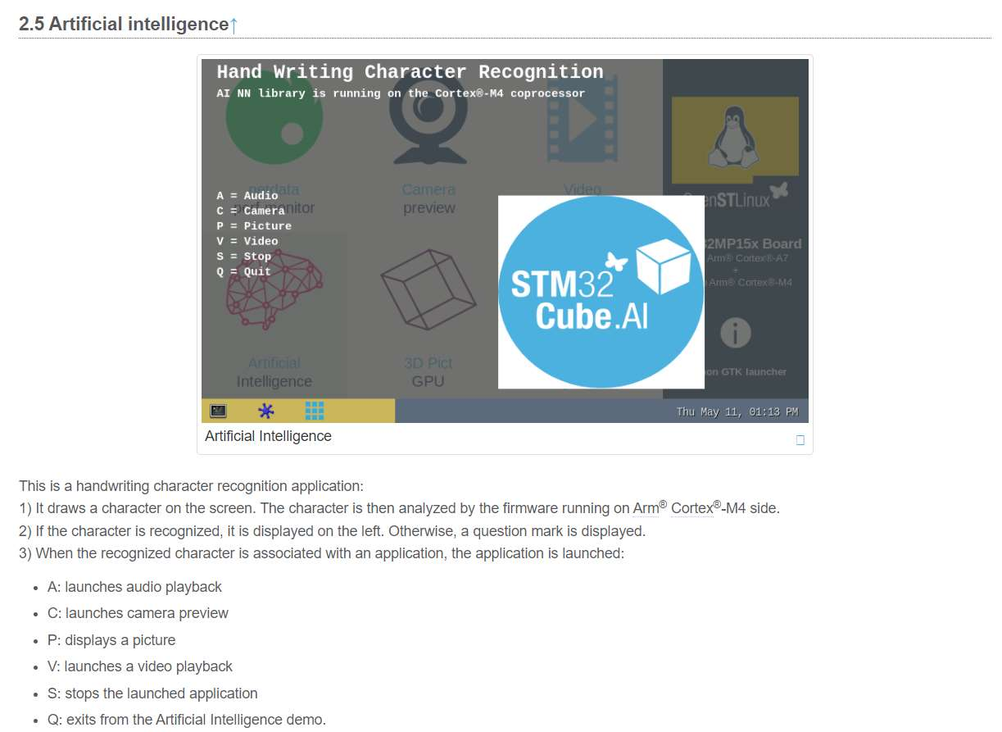
[picture p76: figure]

STM MP1 Package + X-Linux-AI (ARM Cortex -M) Model for Heart Disease Prediction

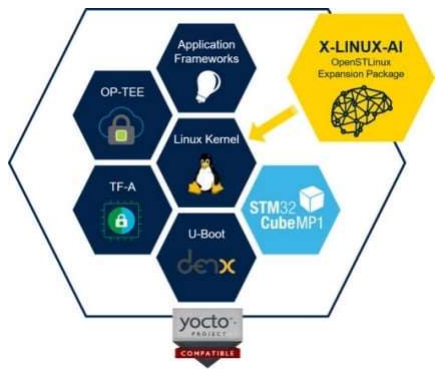
[picture p77: figure]
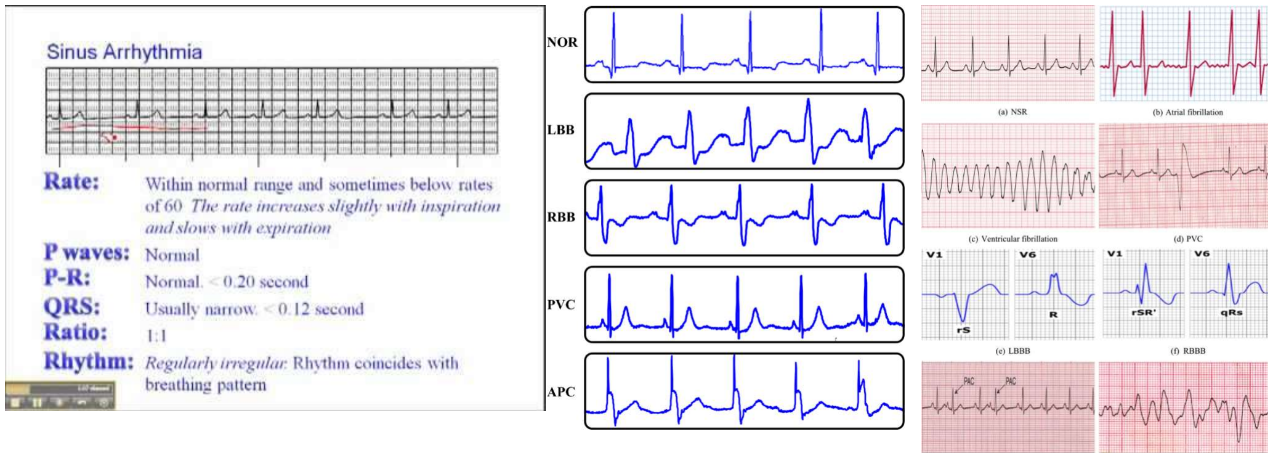
[picture p78: figure]

Identification of Arrhythmia: - Left Bundle Branch Block

- Normal - Premature Atrial Contraction
- Premature Ventricular Contractions
- Right Bundle Branch Block
- Ventricular Fibrillation Dataset: https://github.com/TriparnoChatterjee/Heart_Disease_Prediction_Using_ECG_Images

https://www.kaggle.com/datasets/erhmrai/ecg-image-datahttps://www.kaggle.com/datasets/mohamedeldakrory8/ecg-heart-categorization-dataset-image-version

# Défense Presentation

Sunday, 5 November, 2023 7:51 PM

FYP Page 1

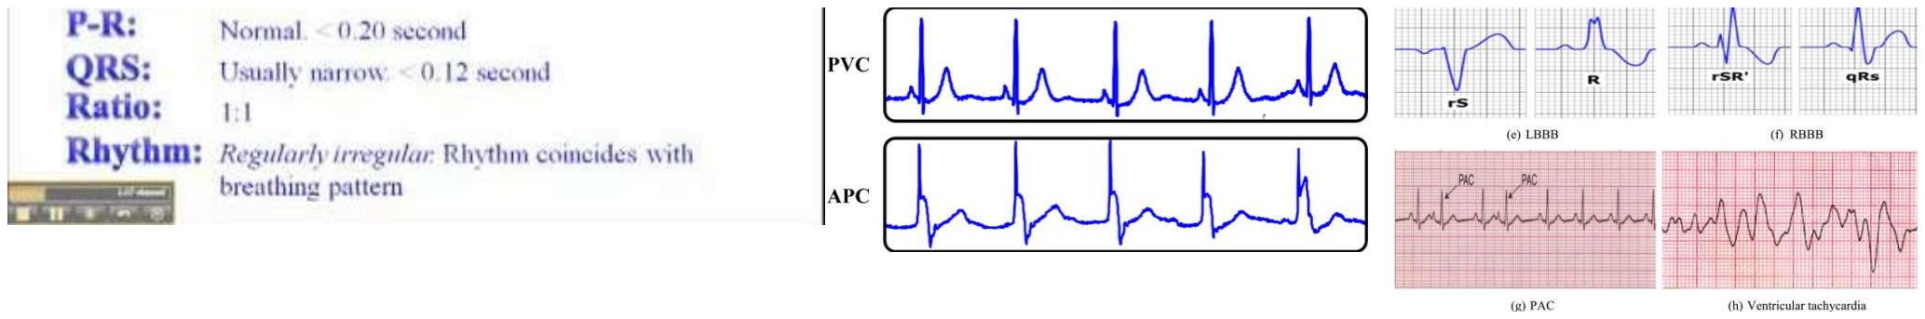
[picture p79: figure]

- Ventricular Fibrillation Dataset: https://github.com/TriparnoChatterjee/Heart_Disease_Prediction_Using_ECG_Images

https://www.kaggle.com/datasets/erhmrai/ecg-image-datahttps://www.kaggle.com/datasets/mohamedeldakrory8/ecg-heart-categorization-dataset-image-version

## Model for Emotion Recognition

Type of Emotions: - Discrete Emotional Model (DEM) -> happy, sad, angry, fear, etc. - Affective Dimensional Model (ADM) -> valence, arousal, dominance

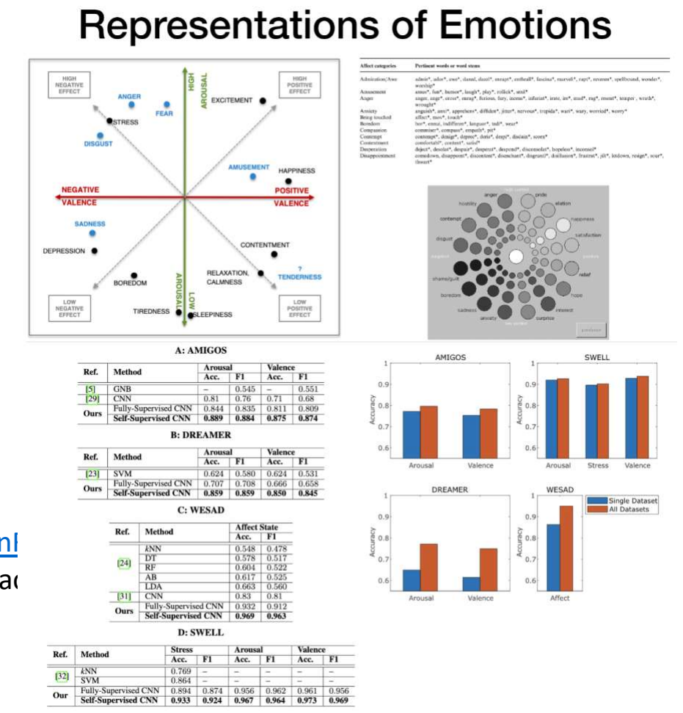
[picture p80: figure]

- Binary Emotional Model -> negative, positive Dataset: 1. Amigos (http://www.eecs.qmul.ac.uk/mmv/datasets/amigos/download.html) 2. Dreamer (https://zenodo.org/records/546113#.YKLY0WYzaHs) 3. Wesad (https://archive.ics.uci.edu/dataset/465/wesad+wearable+stress+and+affect+detection) 4. Case (https://github.com/nosa999/Emotion-Recognition-from-ECG-Signal/blob/main/Case_ECG_EmotionRecognition.py) 5. https://www.kaggle.com/code/danielfesalbon/ecg-signals-emotion-recognition (Model display low accuracy) Architecture: CNN: https://github.com/joergsimon/SSL-ECG-Paper-Reimplementaton/tree/main
- Pytorch
- include DEAP (EEG data)

X-Linux-AI Overview: https://www.st.com/en/embedded-software/x-linux-ai.html

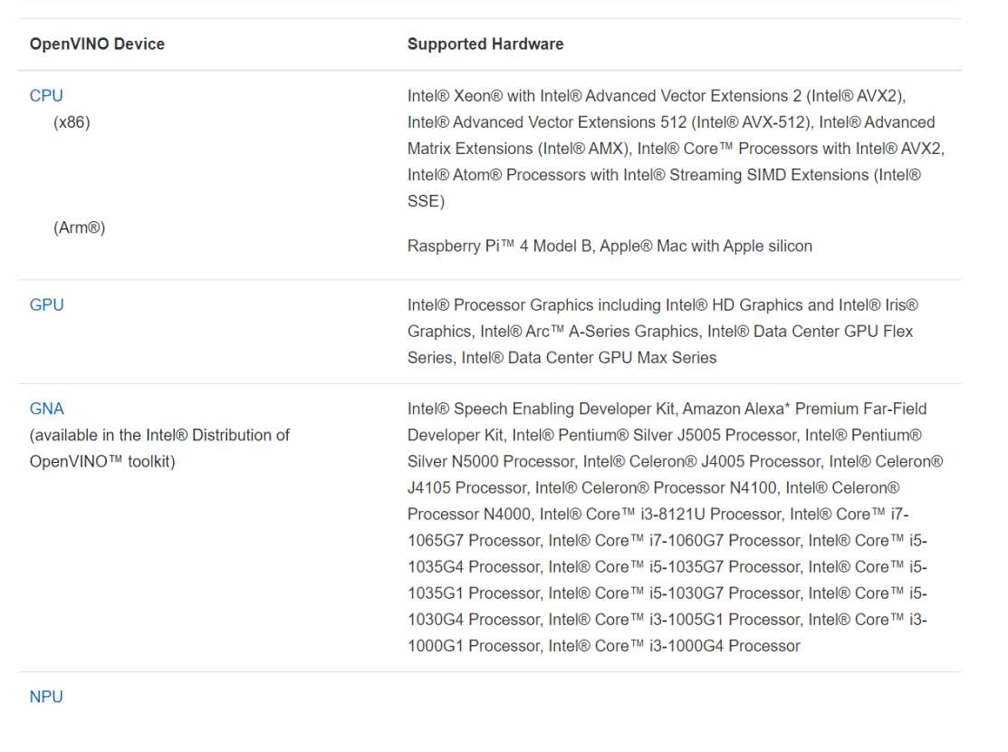
[picture p81: figure]

XNNPACK TensorFlow Lite - Leveraging CPU for ML inference: https://www.st.com/en/embedded-software/x-linux-ai.html

Package Library
https://wiki.st.com/stm32mpu/wiki/X-LINUX-AI_Starter_package

Application
https://wiki.st.com/stm32mpu/wiki/Category:AI_-_Application_exampleshttps://wiki.st.com/stm32mcu/wiki/AI:How_to_use_transfer_learning_to_perform_image_classification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

Initial Idea: Intel OpenVINO (https://docs.openvino.ai/2023.1/openvino_docs_OV_UG_supported_plugins_Supported_Devices.html)

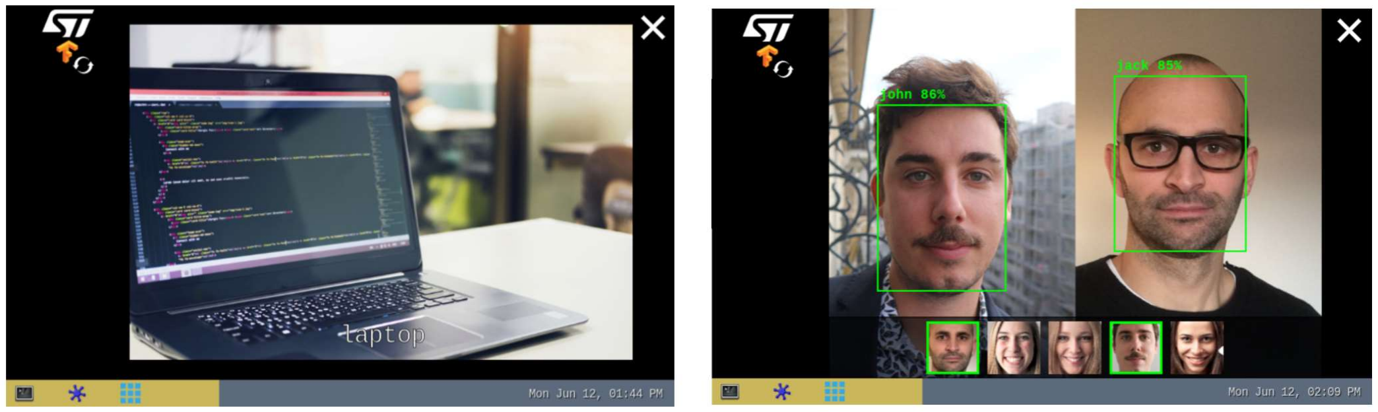
[picture p82: figure]
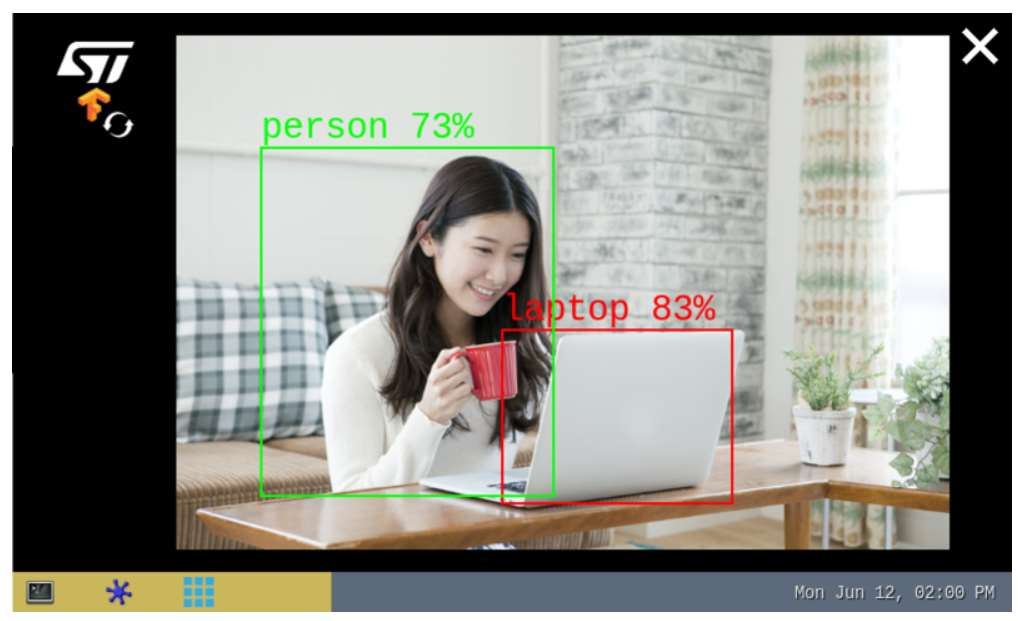
[picture p83: figure]
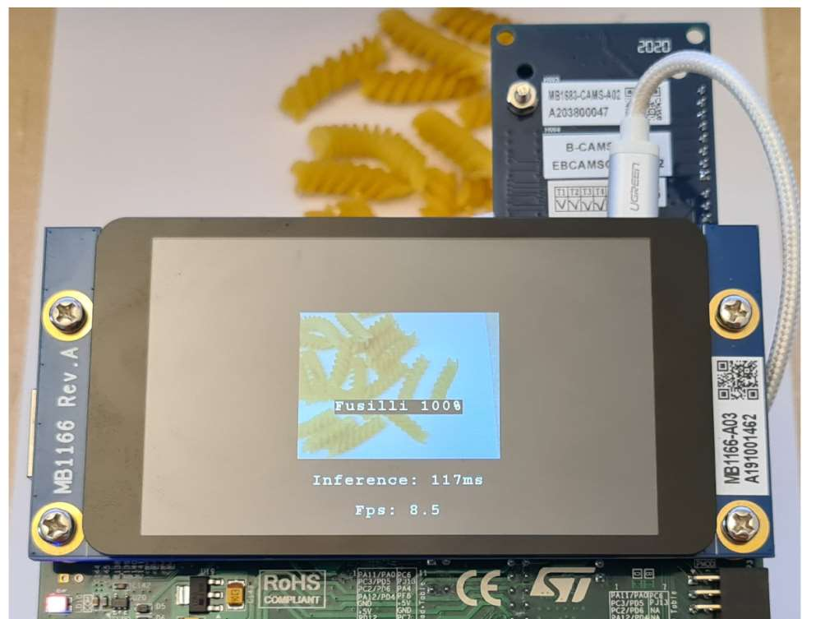
[picture p84: figure]
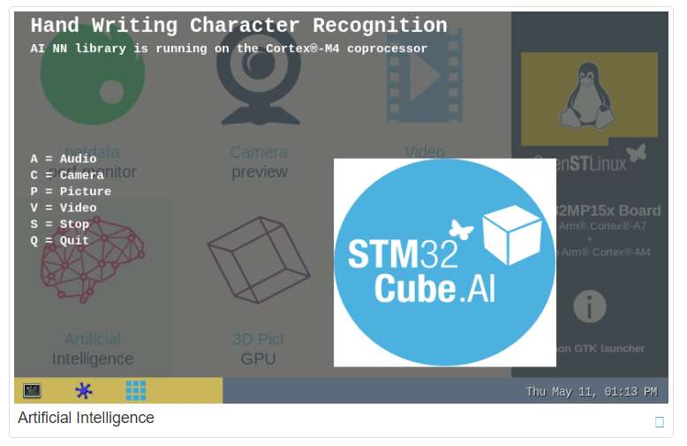
[picture p85: figure]

Cloud Deployment (Optional) Examples: https://github.com/avnet-iotconnect/iotc-python-examples/tree/main/STM32MP157F-DK2_Demo

https://docs.iotconnect.io/iotconnect/git-resource/avnet-iotconnect-repository/https://github.com/STMicroelectronics/meta-predmnt

FYP Page 2 https://www.st.com/resource/en/product_presentation/dsh-predmnt_getting_started.pdf Running on: AWS

FYP Page 3
