xian-cong/Final-Year-Project-Nottingham/links and documents/weekly meeting/Meeting Record Sheet 2023-2024 Template.docx

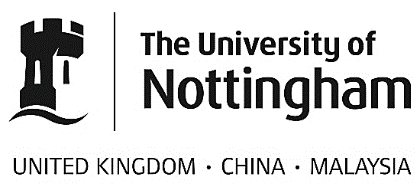
[picture p86: figure]

2023-2024

Student Name(s) :

Project Title :

Supervisor(s) :

Date of meeting : Length of meeting :

Progress made since the last meeting

Items discussed /planned for the week

Remarks (if any)

Student’s signature:

Supervisor’s signature(s) : Date:
