xian-cong/Final-Year-Project-Nottingham/3d model/2s-3s-4s-boost-lipo-liion-charger-ddtccrub-1.snapshot.1/DDTCCRUB CN330X.jpeg

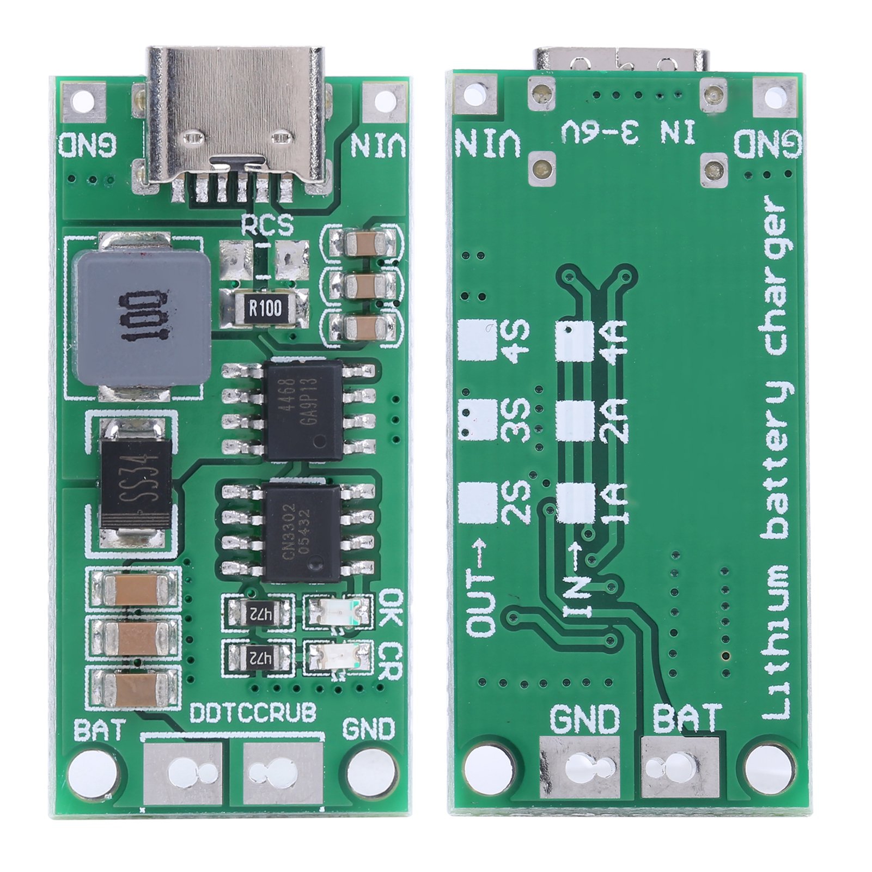
3d model/2s-3s-4s-boost-lipo-liion-charger-ddtccrub-1.snapshot.1/DDTCCRUB CN330X.jpeg
