xian-cong/Final-Year-Project-Nottingham/3d model/ad8232-1.snapshot.1/AD8232_Heart_Rate_Monitor v4.png

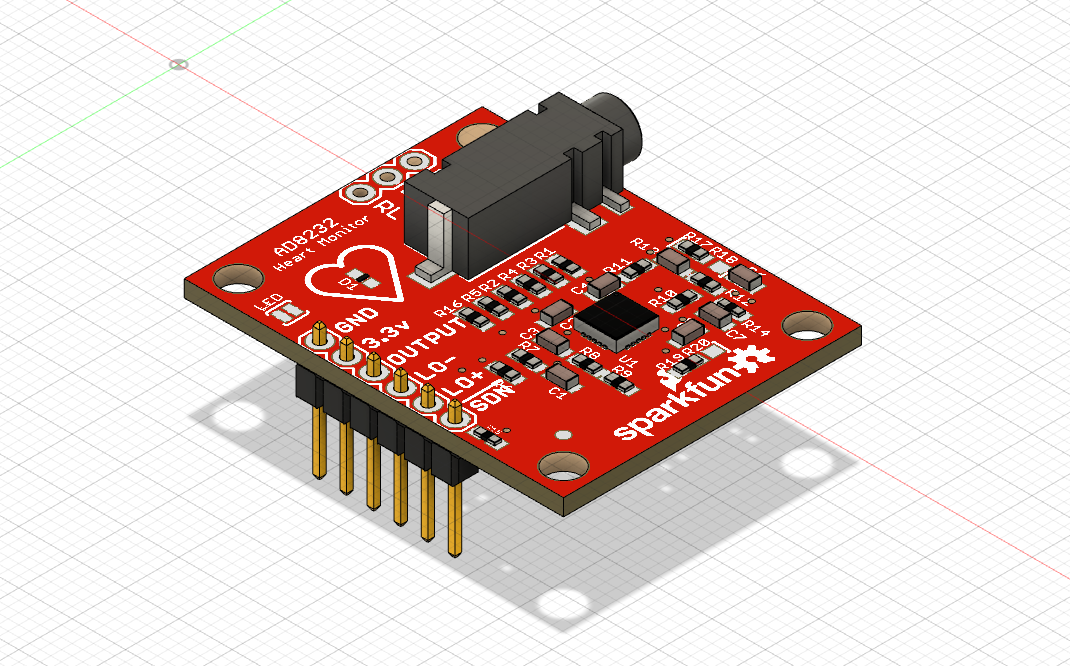
3d model/ad8232-1.snapshot.1/AD8232_Heart_Rate_Monitor v4.png
